svenpetersen1965/C64-Diagnostic-Rev.-586220-Harness/Diag586220_Harness/C128_Keyboard_PCB/Rev. 1/Text/145_cover_sheet.docx

Project Documentation

C128 Diagnostic – Keyboard PCB

Project number: 145

Revision: 1

Date: 15.05.2020
