svenpetersen1965/C64-Diagnostic-Rev.-586220-Harness/Diag586220_Harness/Diag586220_Keyboard_ext/Rev. 0/Texts/Diag586220_Keyb_Ext_ModD.docx

Diagnostic 586220 Harness - Keyboard Dongle Extended Rev. 0

Module Description

# Introduction

The extended Keyboard Dongle is meant to be an extension to existing Diagnostic Harnesses. It prevents the false OK when testing the control ports, while the keyboard PCB is inserted. This is accomplished by analog switches for the feedbacks, that are in common with the joystick signals on the control ports.

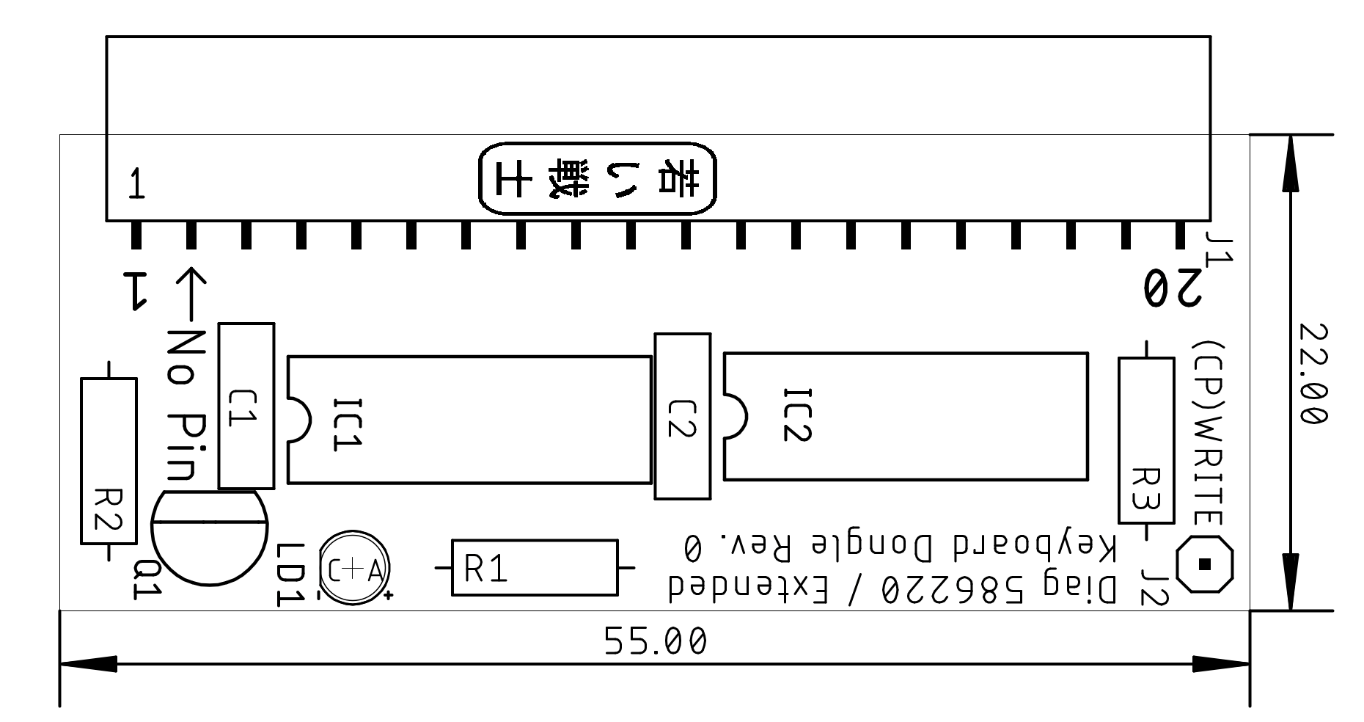
[picture p32: figure]

Figure 1: Dimensions of the PCB

The extended Keyboard Dongle for Diagnostic 586220 provides the required feedback connections for testing the C64’s CIA U1, which the keyboard is connected to. An LED serves as an alternative power and operation indicator. It is normally on and switches off while testing the Control Ports.

The Restore key is connected to a dedicated line and is not tested.

What does Extended Keyboard PCB do better than the normal keyboard PCB?

As long as the old keyboard dongle is connected to the keyboard header, the feedbacks bridge the analog switches for testing the control ports. These analog switches are found on the User Port PCB. They are inside the two 4066 ICs there.

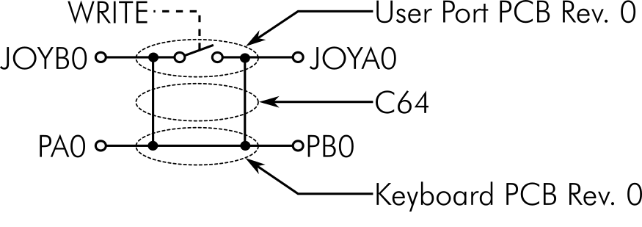
[picture p33: figure]

Figure 2: Test situation with the original diagnostic harness

For properly testing the control ports, the keyboard dongle has to be removed. This way, the test actually requires two passes. Otherwise, the control ports are tested improperly. A broken trace to the control port or a defective port connector would not be detected.

The extended Keyboard Dongle provides switched feedbacks for the signals, that are shared with the joysticks.

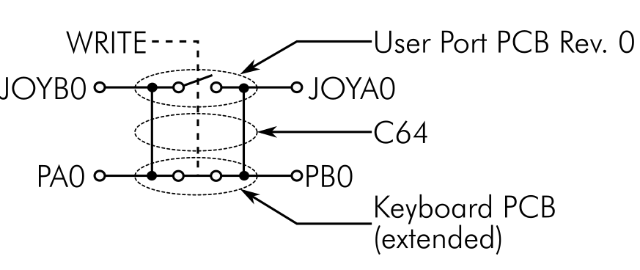
[picture p34: figure]

Figure 3: Test situation with the extended Keyboard Dongle

These are PB0«PA0, PB1«PA1, PB2«PA2, PB3«PA3 and PB4«PA4. The switches are opened by a (cassette port) WRITE signal going high, which also closes the connection on the user port dongle at the same time. The reason is, that

This WRITE signal is generated via a voltage divider on the user Port Dongle, which is also fed back to the Cassette Port Dongle. It can be found on Pin 5 of the cassette edge connector (on every kind of test harness). An existing harness can be easily modified by soldering a 40cm Dupont cable to the indicated Pin (refer to Figure 4), which is then connected to J2 (one pin) of the extended Keyboard Dongle.

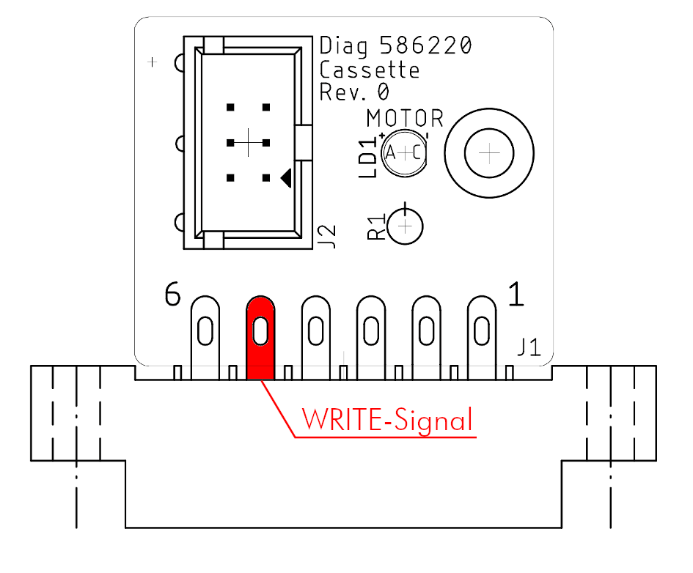
[picture p35: figure]

Figure 4: Locating the Write signal

In case this cable is not connected, the extended Keyboard Dongle works like a normal keyboard dongle. The analog switches are closed in this case. The open state of the switches is indicated by the LED, which is off while testing the control ports (this needs to be observed).

The extended Keyboard Dongle works with all versions of the standard Diagnostic 586220 software. A modification of the software is not required.

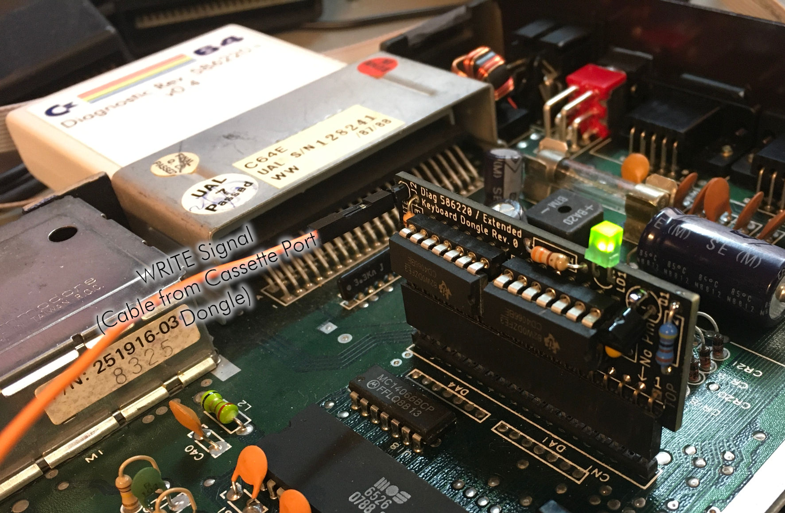
[picture p36: figure]

Figure 5: The Extended Keyboard Dongle on an ASSY 250469

# Connections

J1: 20p receptacle (pitch 2.54mm)

Pin | Signal | | Signal | Pin
5 | PB3 | « | PA3 | 17
6 | PB6 | « | PA6 | 14
7 | PB5 | « | PA5 | 15
8 | PB4 | « | PA4 | 16
9 | PB7 | « | PA7 | 20
10 | PB2 | « | PA2 | 18
11 | PB1 | « | PA1 | 19
12 | PB0 | « | PA0 | 13

J2: Single pin (DuPont). Input for the WRITE signal from the Cassette Port (Dongle).

Diag586220_Keyb_Ext_ModD.docx 10.03.2020 20:10 Drafted by Sven Petersen Page 2 of 2 Doc.-No.: 143-6-01-00

Diag586220_Keyb_Ext_ModD.docx 10.03.2020 20:10 Drafted by Sven Petersen Page 1 of 1 Doc.-No.: 143-6-01-00
