svenpetersen1965/C64-Diagnostic-Rev.-586220-Harness/Diag586220_Harness/Diag586220_Keyboard_ext/Rev. 0/Texts/143_cover_sheet.docx

Project Documentation

Diagnostic Rev. 586220 – Extended Keyboard Dongle

Project number: 143

Revision: 0

Date: 16.02.2020
