svenpetersen1965/C64-Diagnostic-Rev.-586220-Harness/Diag586220_Harness/C128_Keyboard_PCB/SMD_Rev. 1/Pictures/dimensions.png

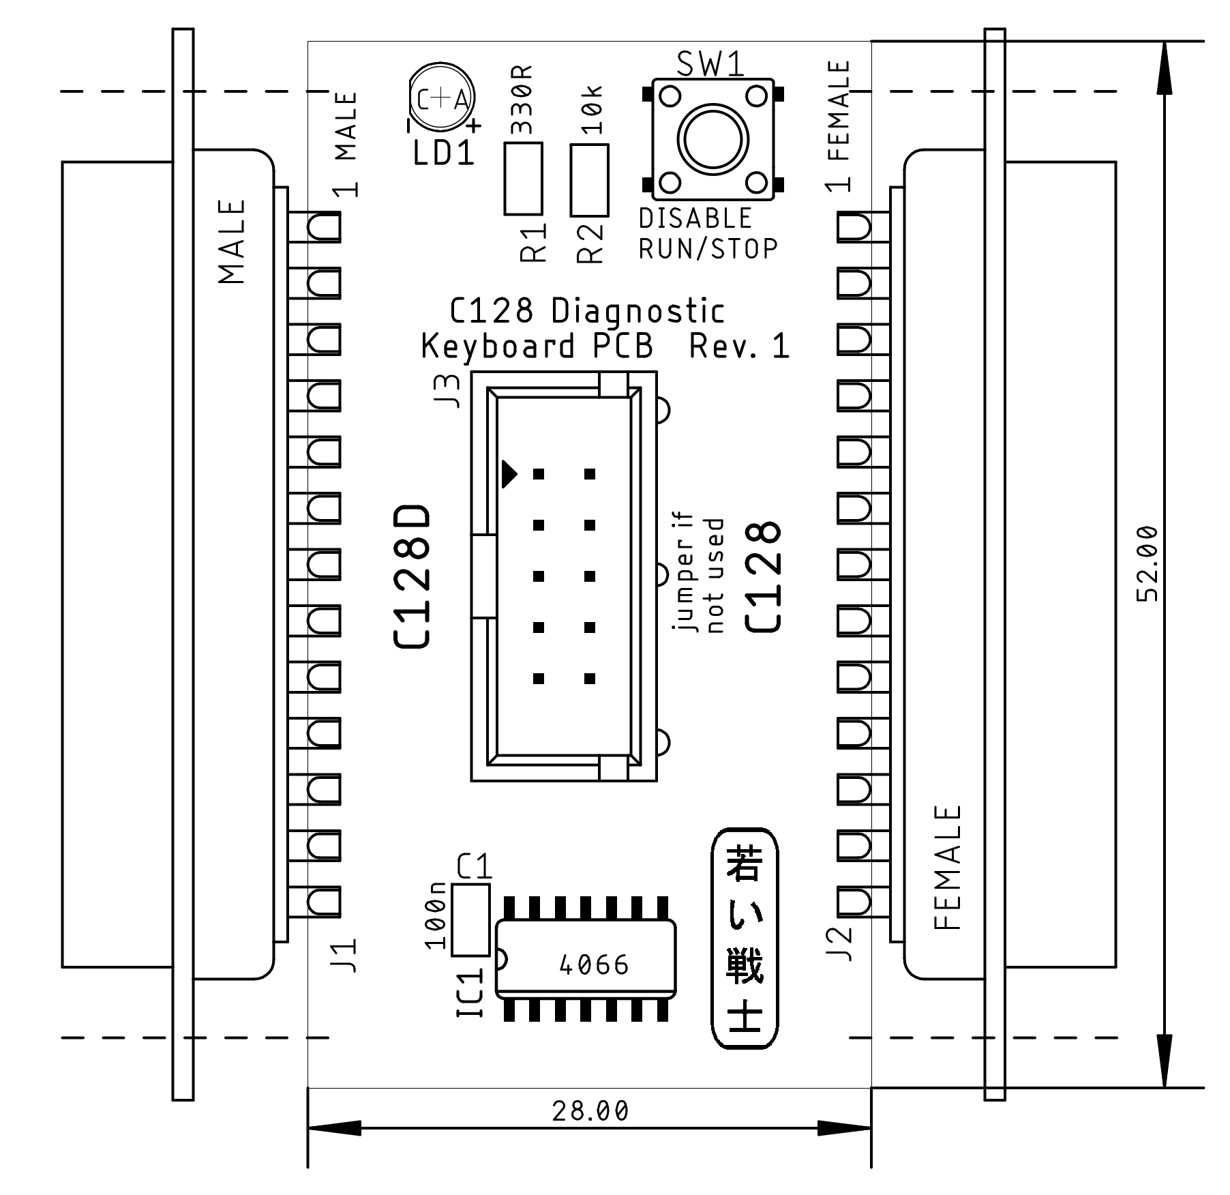
Diag586220_Harness/C128_Keyboard_PCB/SMD_Rev. 1/Pictures/dimensions.png
