svenpetersen1965/C64-Diagnostic-Rev.-586220-Harness/Diag586220_Harness/Case_3D_Data/Cassette Port/Rev. 0/picture/Diag_CP v5.png

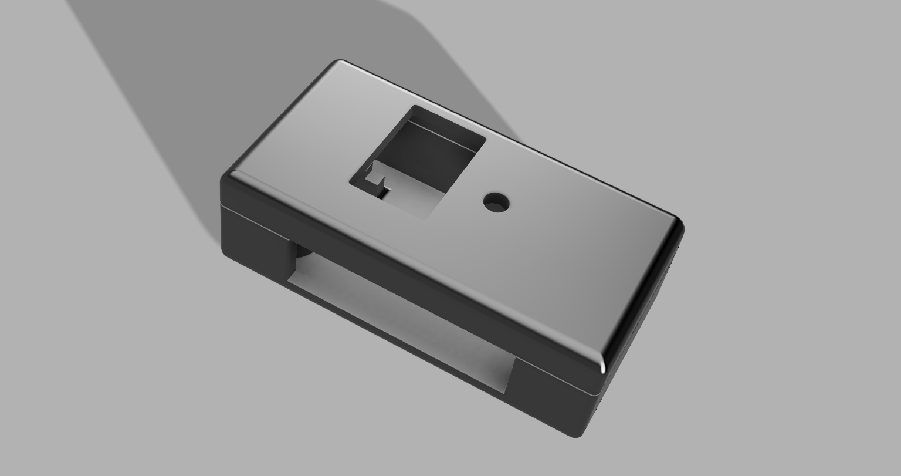
Diag586220_Harness/Case_3D_Data/Cassette Port/Rev. 0/picture/Diag_CP v5.png
