svenpetersen1965/C64-Diagnostic-Rev.-586220-Harness/Diag586220_Harness/Case_3D_Data/Label/Rev. 0/Inkscape/Case_Labels.png

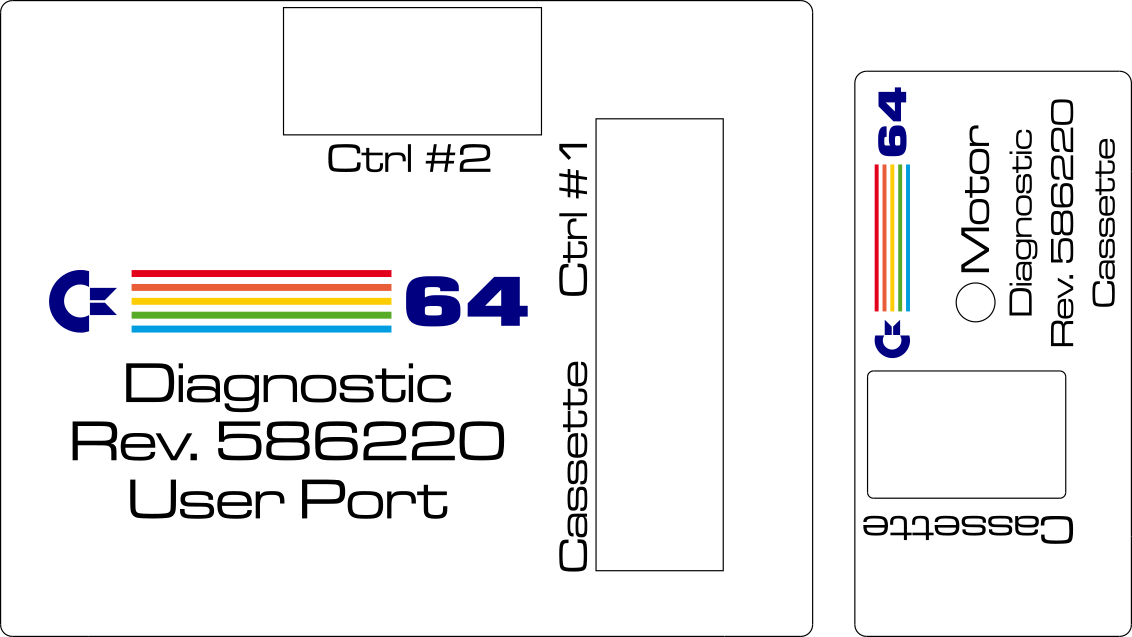
Diag586220_Harness/Case_3D_Data/Label/Rev. 0/Inkscape/Case_Labels.png
