svenpetersen1965/C64-Diagnostic-Rev.-586220-Harness/Diag586220_Harness/Case_3D_Data/Label/Rev. 1/Rev. 1.0/picture/user_port_label.png

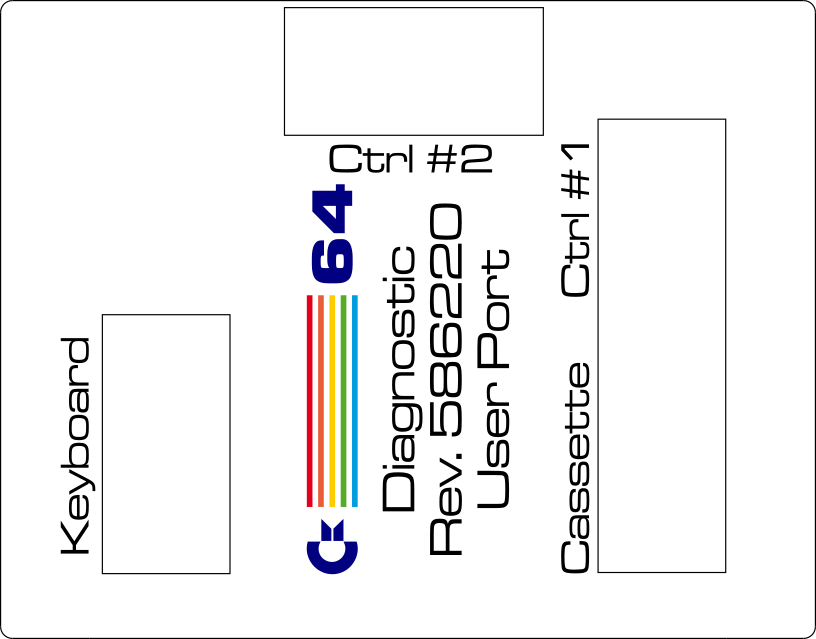
Diag586220_Harness/Case_3D_Data/Label/Rev. 1/Rev. 1.0/picture/user_port_label.png
