svenpetersen1965/C64-Diagnostic-Rev.-586220-Harness/Diag586220_Harness/Case_3D_Data/Label/Rev. 1/Rev. 1.1/picture/case labels.png

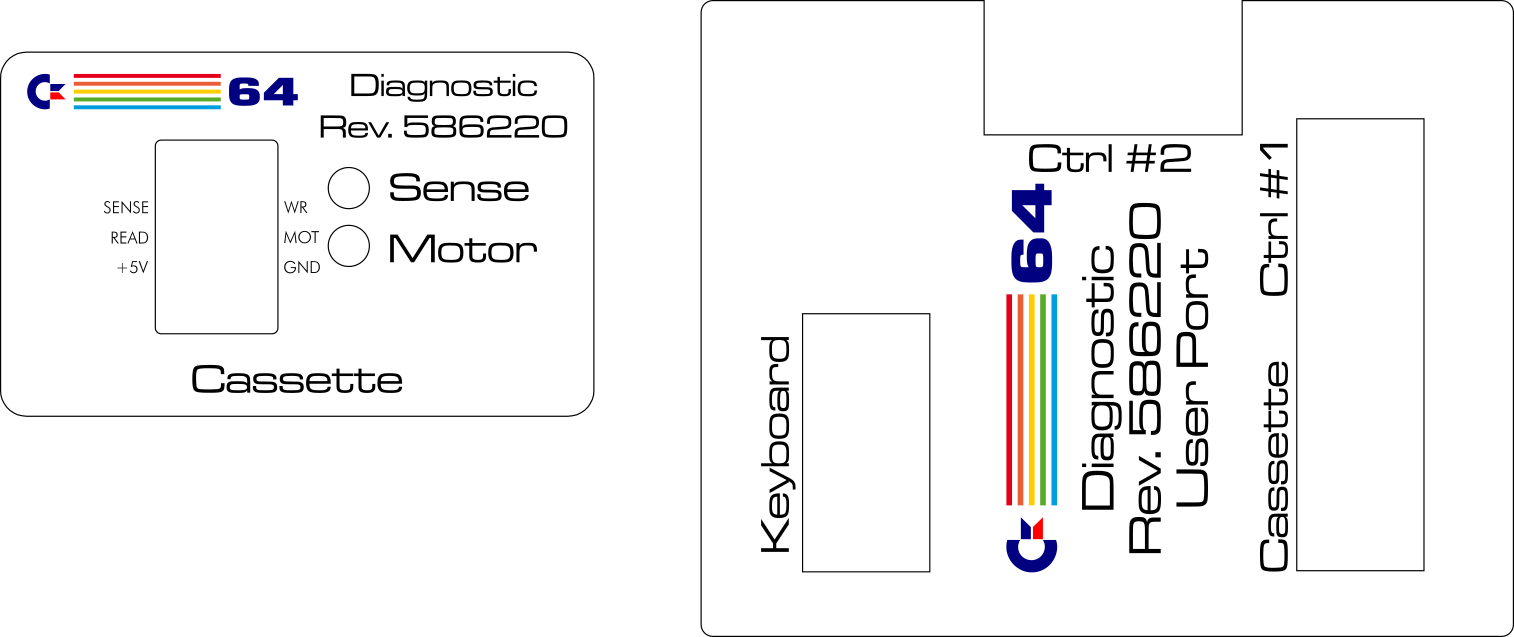
Diag586220_Harness/Case_3D_Data/Label/Rev. 1/Rev. 1.1/picture/case labels.png
