svenpetersen1965/C64-Diagnostic-Rev.-586220-Harness/Diag586220_Harness/Case_3D_Data/Label/Rev. 3/Pictures/label_VM.png

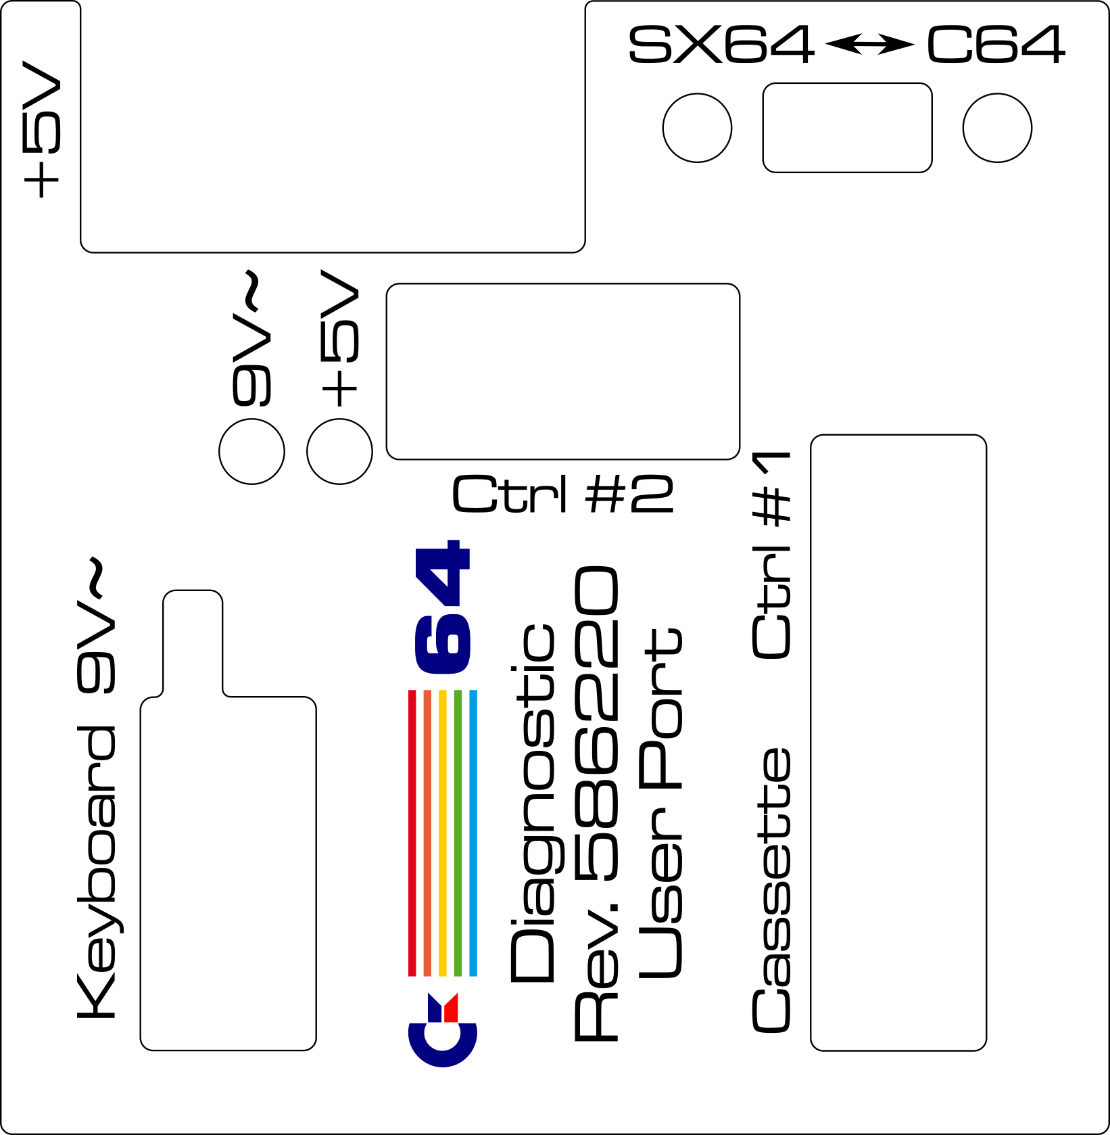
Diag586220_Harness/Case_3D_Data/Label/Rev. 3/Pictures/label_VM.png
