svenpetersen1965/C64-Diagnostic-Rev.-586220-Harness/Diag586220_Harness/Case_3D_Data/User Port/Rev. 0/Picture/Diag_UP v8.png

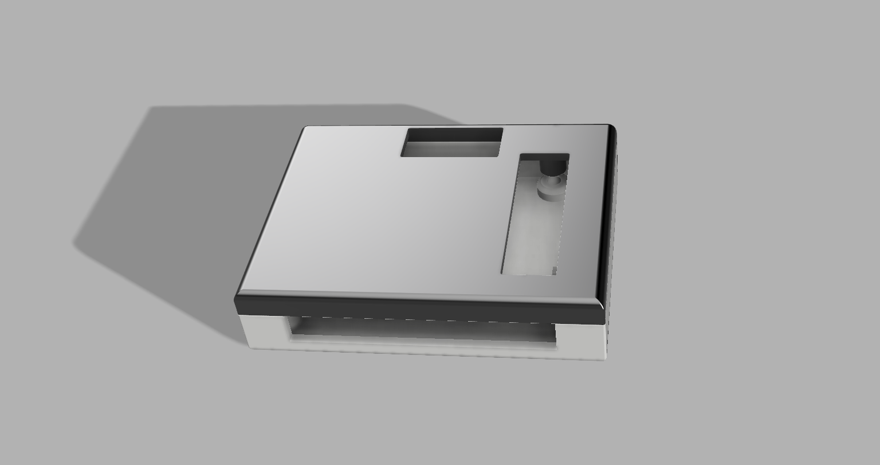
Diag586220_Harness/Case_3D_Data/User Port/Rev. 0/Picture/Diag_UP v8.png
