svenpetersen1965/C64-Diagnostic-Rev.-586220-Harness/Diag586220_Harness/Case_3D_Data/User Port/Rev. 3/Inkscape/7segVM.png

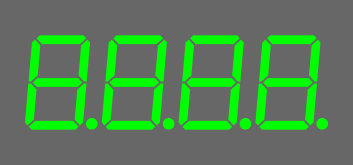
Diag586220_Harness/Case_3D_Data/User Port/Rev. 3/Inkscape/7segVM.png
