svenpetersen1965/C64-Diagnostic-Rev.-586220-Harness/Diag586220_Harness/Case_3D_Data/User Port/Rev. 3/pictures/Diag_UP_PCB_v3 v24.png

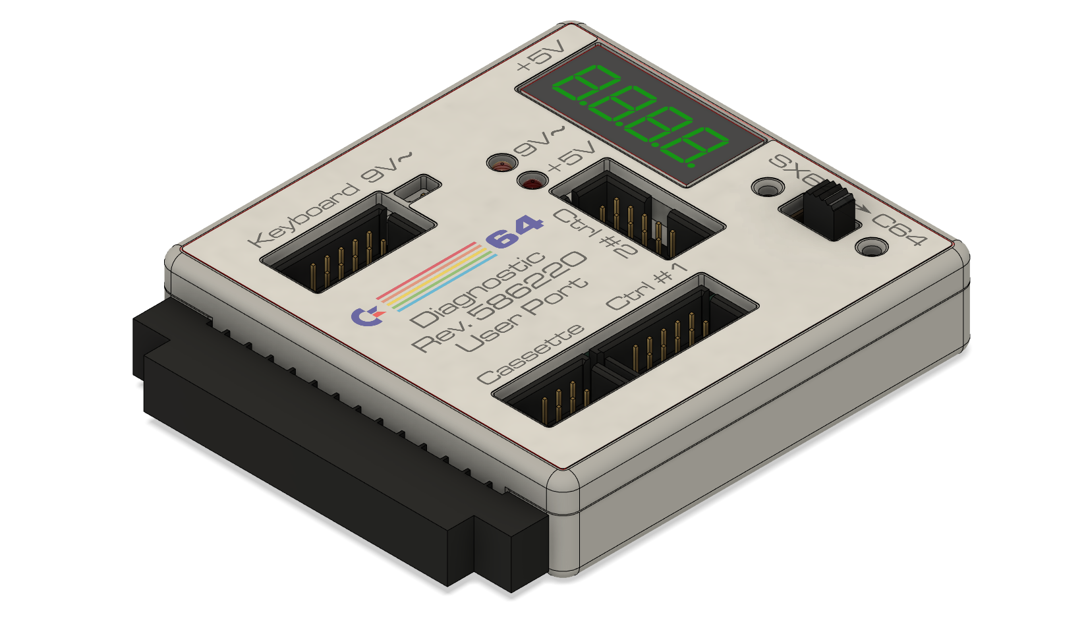
Diag586220_Harness/Case_3D_Data/User Port/Rev. 3/pictures/Diag_UP_PCB_v3 v24.png
