svenpetersen1965/C64-Diagnostic-Rev.-586220-Harness/Diag586220_Harness/Diag586220_Cassette_Port/SMD_Rev.1/pictures/cassette_pcb.png

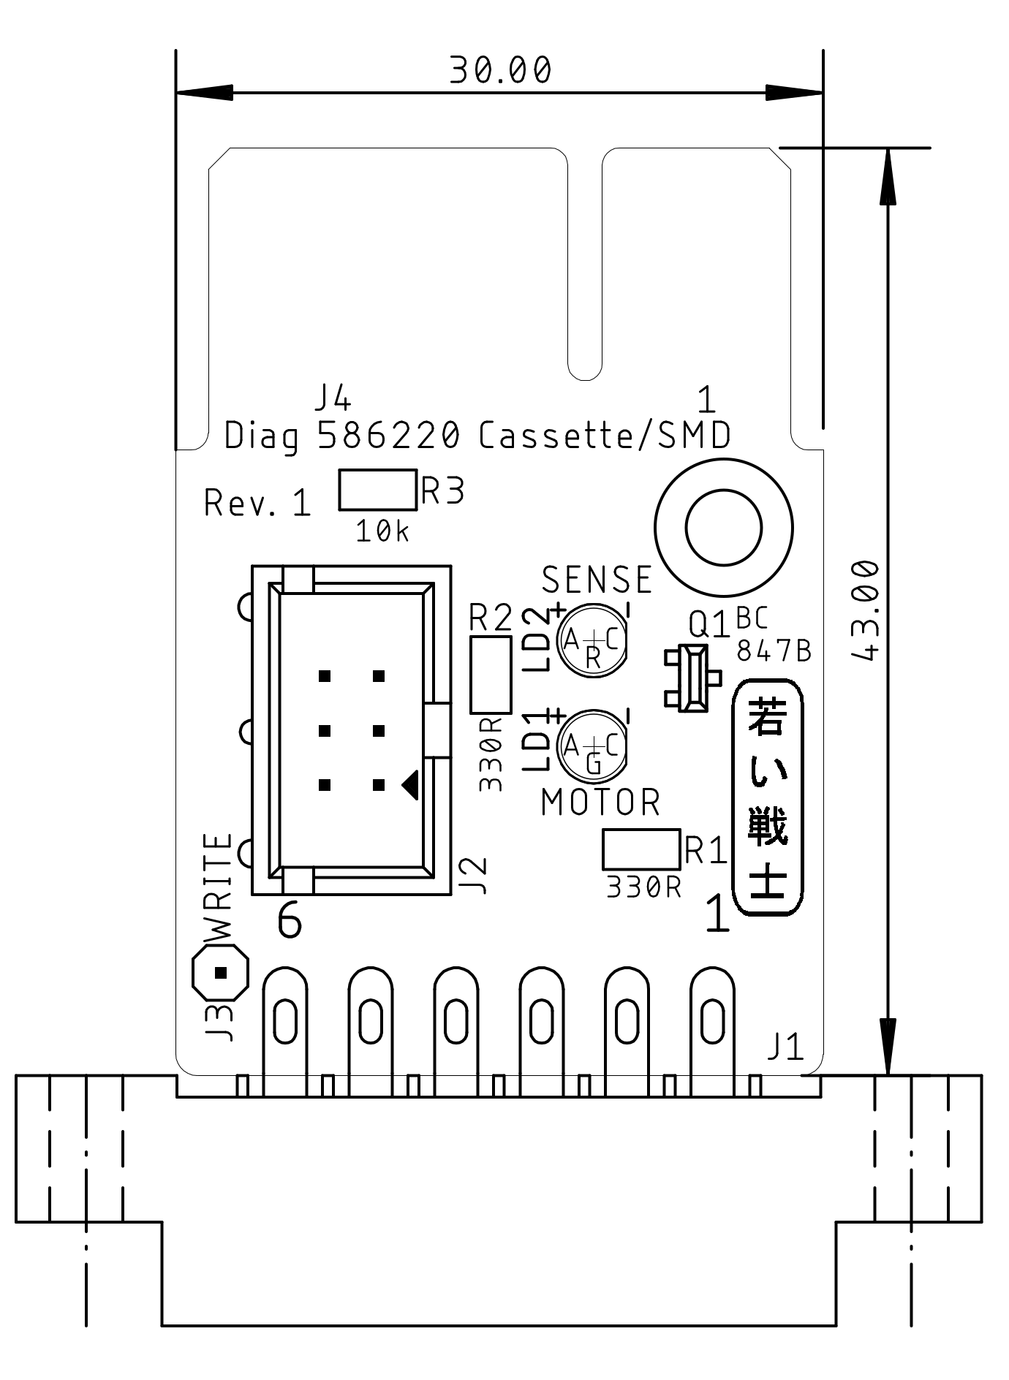
Diag586220_Harness/Diag586220_Cassette_Port/SMD_Rev.1/pictures/cassette_pcb.png
