svenpetersen1965/C64-Diagnostic-Rev.-586220-Harness/Diag586220_Harness/Diag586220_Keyboard_ext/Rev. 0/pictures/4032_-_Modification_Rev_0.JPG

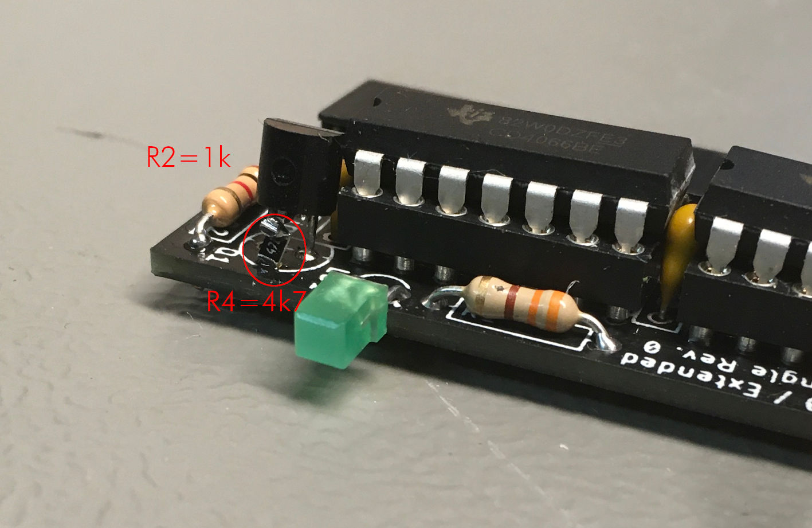
Diag586220_Harness/Diag586220_Keyboard_ext/Rev. 0/pictures/4032_-_Modification_Rev_0.JPG
