svenpetersen1965/C64-Diagnostic-Rev.-586220-Harness/Diag586220_Harness/Diag586220_Keyboard_ext/Rev. 1/Texts/4199_-_Ext_KB_Dongle_Rev1.JPG

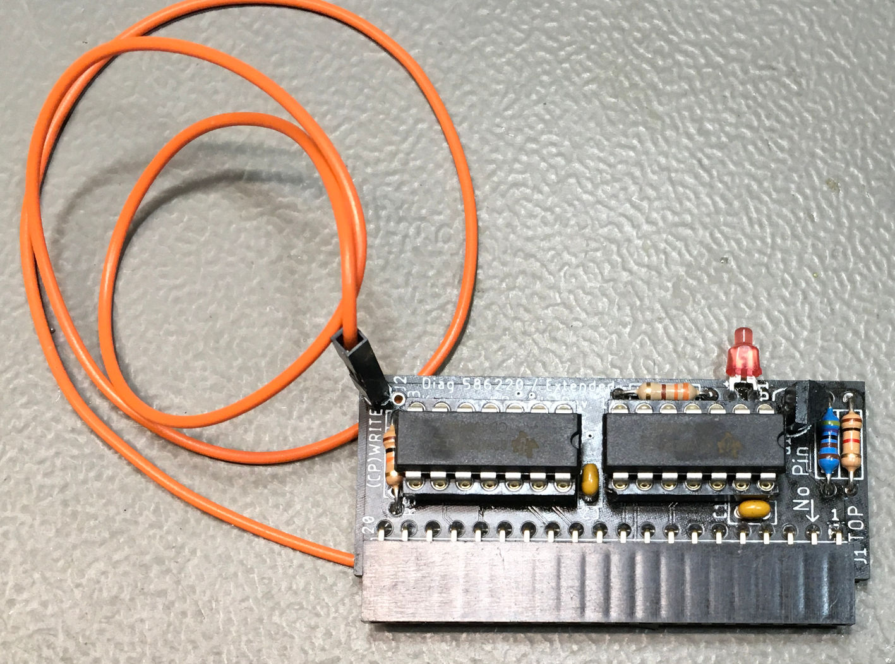
Diag586220_Harness/Diag586220_Keyboard_ext/Rev. 1/Texts/4199_-_Ext_KB_Dongle_Rev1.JPG
