svenpetersen1965/C64-Diagnostic-Rev.-586220-Harness/Diag586220_Harness/Diag586220_User_Port/Rev.3/AutoSketch/IEC-Dongle.gif

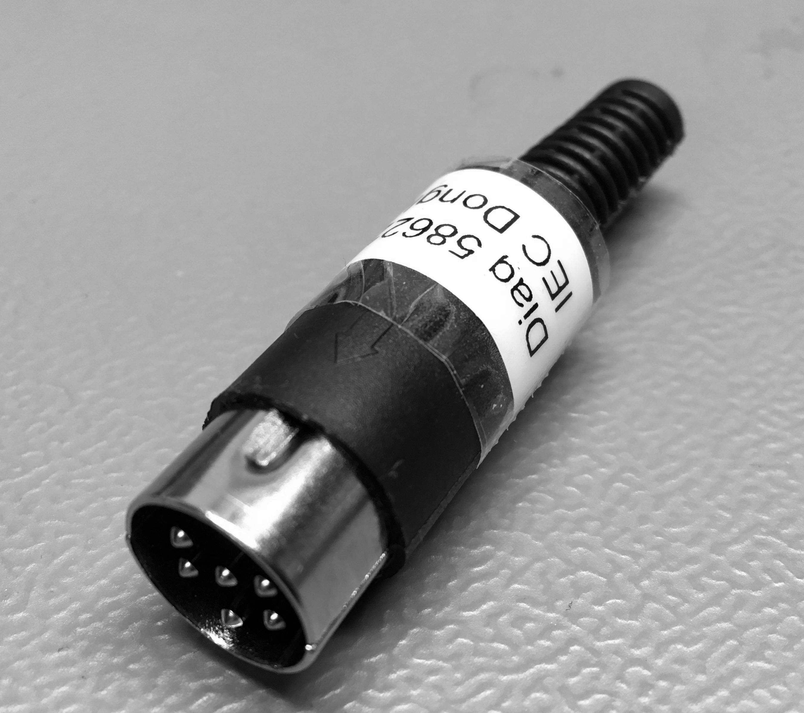
Diag586220_Harness/Diag586220_User_Port/Rev.3/AutoSketch/IEC-Dongle.gif
