svenpetersen1965/C64-Diagnostic-Rev.-586220-Harness/Diag586220_Harness/Diag586220_User_Port/Rev.3/pictures/1520_-_4digit_VM_in_situ.JPG

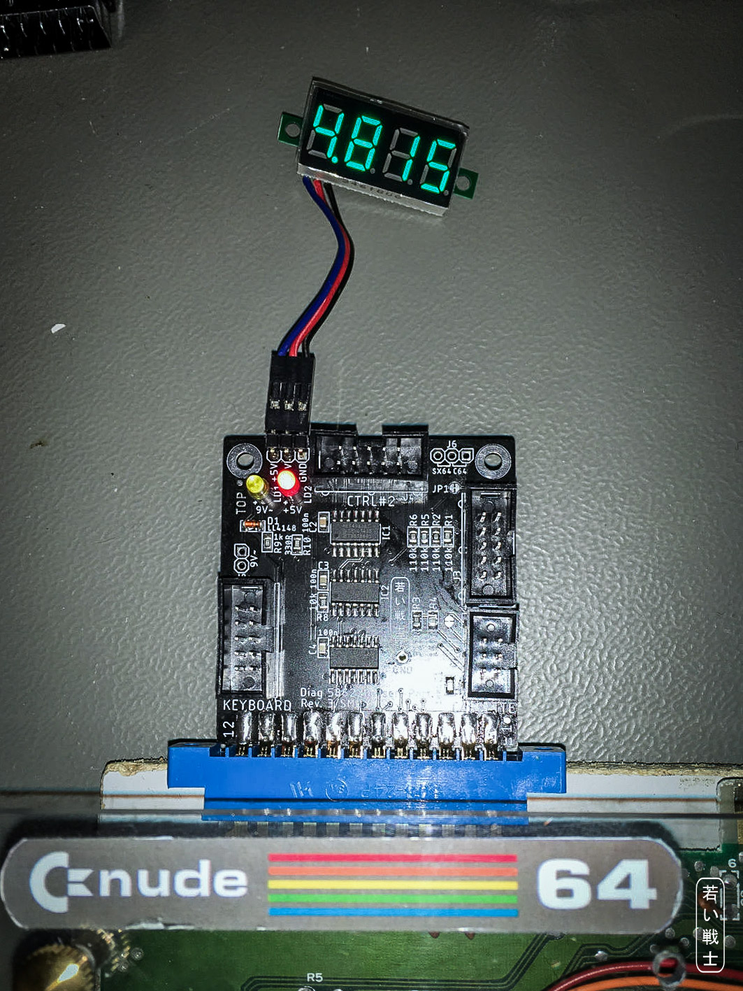
Diag586220_Harness/Diag586220_User_Port/Rev.3/pictures/1520_-_4digit_VM_in_situ.JPG
