svenpetersen1965/C64-Diagnostic-Rev.-586220-Harness/Diag586220_Harness/Diag586220_User_Port/Rev.3/pictures/4961_-_C64_Diagnostic_Harvness_VM.JPG

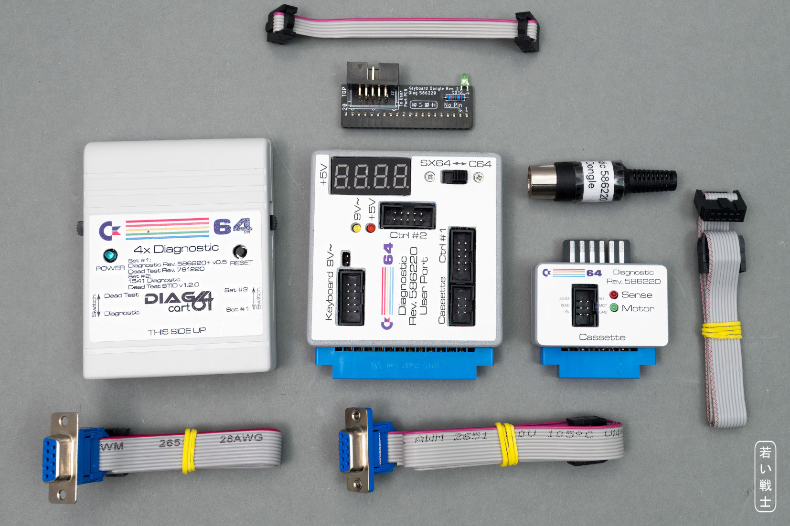
Diag586220_Harness/Diag586220_User_Port/Rev.3/pictures/4961_-_C64_Diagnostic_Harvness_VM.JPG
