svenpetersen1965/C64-Diagnostic-Rev.-586220-Harness/Diag586220_Harness/Diag586220_User_Port/Rev.3/pictures/9290_-_case_with_SX64C64_Jumper_configuration.JPG

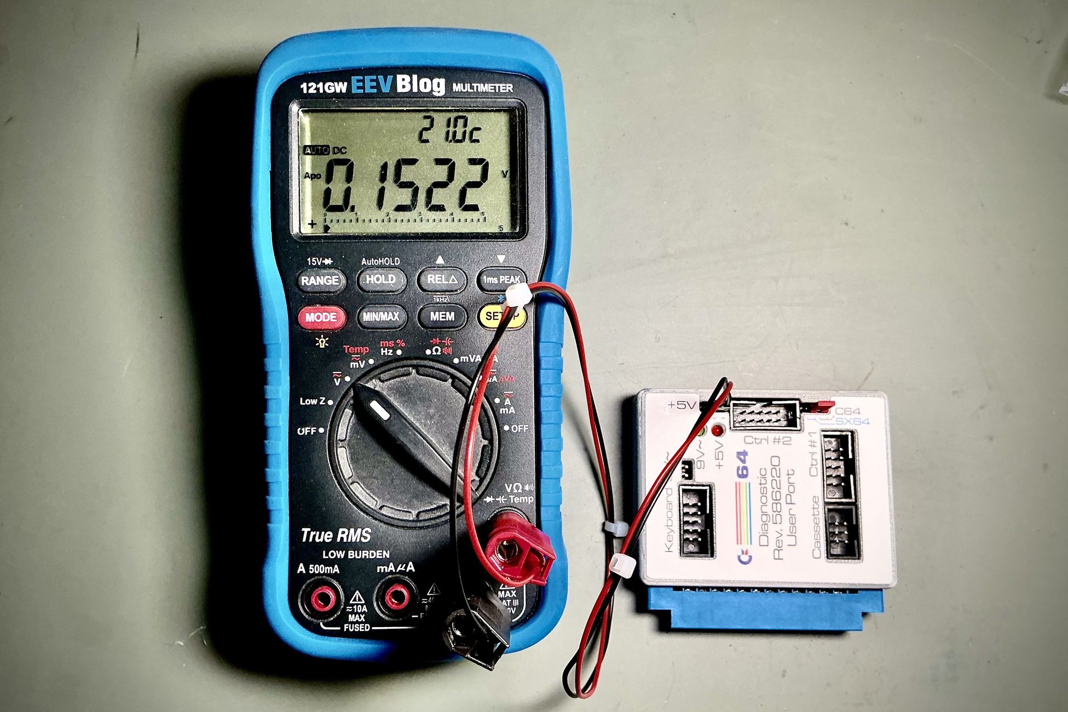
Diag586220_Harness/Diag586220_User_Port/Rev.3/pictures/9290_-_case_with_SX64C64_Jumper_configuration.JPG
