svenpetersen1965/C64-Diagnostic-Rev.-586220-Harness/Diag586220_Harness/Diag586220_User_Port/SMD_Rev.3/pictures/IMG_2500_1.JPG

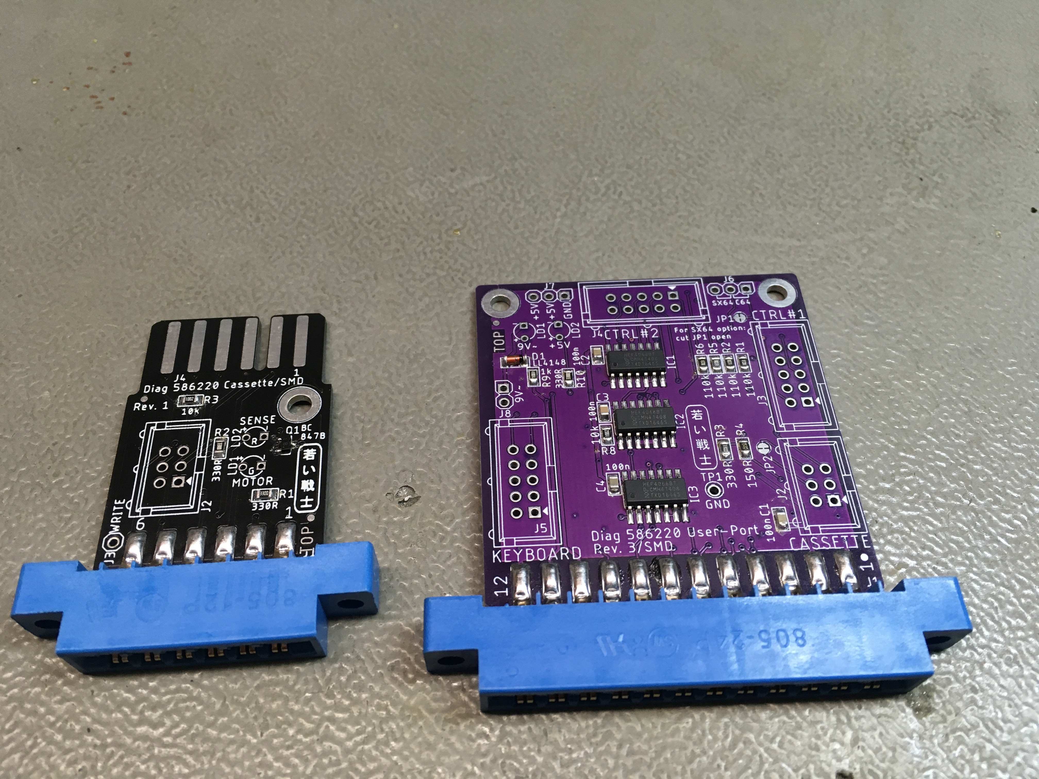
Diag586220_Harness/Diag586220_User_Port/SMD_Rev.3/pictures/IMG_2500_1.JPG
