svenpetersen1965/C64-Diagnostic-Rev.-586220-Harness/Diag586220_Harness/calculation/Diag_Harness_Rev1_complete_calc.xlsx

Calculation Diagnostic Harness Rev. 1
Pos. | Qty | Value | €/ea | € | Comment
1 | 1 | Cassette Port Dongle | 1.00 € | 1.00 € | 2 layer, Cu 35µ, HASL, 30.0mm x 25.0mm, 1.6mm FR4
2 | 1 | 2x6, 3.96mm pitch | 3.00 € | 3.00 € | edge connector, C64 cassette port
3 | 1 | 2x3 box connector | 0.19 € | 0.19 € | e.g. Reichelt WSL 6G
4 | 1 | 3mm/green | 0.20 € | 0.20 € | LED, 3mm, green
5 | 1 | 3mm/red | 0.20 € | 0.20 € | LED, 3mm, red
6 | 1 | BC546B | 0.10 € | 0.10 € | Transistor
7 | 2 | 10k | 0.10 € | 0.20 € | 1/4 Watt, 5%
8 | 1 | 330R | 0.10 € | 0.10 € | 1/4 Watt, 5%
 |  |  |  | 4.99 €
Pos. | Qty | Value | €/ea | € | Comment
1 | 1 | User Port Dongle | 1.00 € | 1.00 € | 2 layer, Cu 35µ, HASL, LLL x BBB, 1.6mm FR4
2 | 1 | 2x3 box connector | 0.19 € | 0.19 € | e.g. Reichelt WSL 6G
3 | 3 | 2x5 box connector | 0.10 € | 0.30 € | e.g. Reichelt WSL 10G
4 | 1 | 0R | 0.10 € | 0.10 € | 0 Ohm bridge
5 | 4 | 100n/50V | 0.20 € | 0.80 € | cer. cap, 2.5mm pitch
6 | 4 | 110k | 0.10 € | 0.40 € | 1/4W, 1%
7 | 1 | 150R | 0.10 € | 0.10 € | 1/4W, 5%
8 | 1 | 320R | 0.10 € | 0.10 € | 1/4W, 5% (316W works, 330W should work as well)
9 | 3 | HCF4066B | 0.67 € | 2.01 € | ST Micro or equivalent
10 | 3 | DIL 14 | 0.23 € | 0.69 € | DIL IC sockets
11 | 1 | 2x12, 3.96mm pitch | 3.00 € | 3.00 € | edge connector, C64 user port
12 | 3 | TP 1pin | 0.00 € | 0.00 € | Pin Header, e.g. Reichelt RND 205-00622
13 | 170 | 10p/AWG28/1,27mm | 0.01 € | 0.85 € | Ribbon Cable
14 | 2 | 6p IDC receptable, 2,54mm | 0.63 € | 1.26 € | e.g. Reichelt RND 205-00680
15 | 4 | 10p IDC receptable, 2,54mm | 0.25 € | 1.00 € | e.g. Reichelt RND 205-00682
16 | 2 | 9p D-SUB (female), IDC | 0.66 € | 1.32 € | e.g. Reichelt D-SUB BU 09FB
17 | 1 | DIN-plug 6p | 0.26 € | 0.26 € | e.g. Reichelt MAS 60
18 | 4 | Wire 0,25mm², red | 0.00 € | 0.00 € | wire, color what ever
 |  |  |  | 13.38 €
Pos. | Qty | Value | €/ea | € | Comment
1 | 1 | Keyboard Dongle | 1.00 € | 1.00 € | 2 layer, Cu 35µ, HASL, 53.0mm x 14.0mm, 1.6mm FR4
2 | 1 | BL1-85AXX-20U | 0.45 € | 0.45 € | e.g. MPE Garry, Reichelt BL 1x20W8 2,54
3 | 1 | 3mm/green | 0.20 € | 0.20 € | LED
4 | 1 | 2x5 box connector | 0.10 € | 0.10 € | e.g. Reichelt WSL 10G
5 | 1 | 330R | 0.10 € | 0.10 € | 1/4 Watt, 5%
 |  |  |  | 1.85 €
Pos. | Qty | Value | €/ea | € | Comment
1 | 1 | C128 Keyboard Dongle | 1.00 € | 1.00 € | 2 layer, Cu 35µ, HASL, 28.0 x 48.0mm, 1.6mm FR4
2 | 1 | 2x5pin box header, 2.54mm pitch | 0.10 € | 0.10 € | e.g. Reichelt.de: WSL 10G.
3 | 1 | LED 3mm, green | 0.20 € | 0.20 € | LED, standard
4 | 1 | 330R | 0.10 € | 0.10 € | Resistor, 0.25W, 5% or better
5 | 1 | DB25F/EDGE | 0.22 € | 0.22 € | DSub 25, female, solder cups, e.g. Reichelt.de: D-SUB BU 25
6 | 1 | DB25M/EDGE | 0.26 € | 0.26 € | DSub 25, male, solder cups, e.g. Reichelt.de: D-SUB ST 25
7 | 1 | 10k | 0.10 € | 0.10 € | Resistor, 0.25W, 5% or better
8 | 1 | JTP-1130 | 0.15 € | 0.15 € | Standard 6x6mm tact switch, e.g. Namae JTP-1130 or any other
9 | 1 | HCF4066B | 0.67 € | 0.67 € | ST Micro or equivalent (4066)
10 | 1 | DIL 14 | 0.23 € | 0.23 € | DIL IC sockets
11 | 1 | 100n/50V | 0.20 € | 0.20 € | cer. cap, 2.5mm pitch
 |  |  |  | 3.23 €
