svenpetersen1965/C64-Diagnostic-Rev.-586220-Harness/Diag586220_Harness/Diag586220_User_Port/Rev.3/excel/Diag586220_UserPort_calc_v3_0.xlsx

Diagnostic Rev. 586220 Harness - User Port Rev. 3
Bill of Material Rev. 3.0
Pos. | Qty | Value | €/ea | € | Comment
1 | 1 | 113-2-01-03 | 1.00 € | 1.00 € | 2 layer, Cu 35µ, HASL, LLL x BBB, 1.6mm FR4
2 | 1 | 2x3 box connector | 0.29 € | 0.29 € | e.g. Reichelt WSL 6G
3 | 3 | 2x5 box connector | 0.11 € | 0.33 € | e.g. Reichelt WSL 10G
4 | 0 | ~~0R~~ | 0.10 € | ~~0.00 €~~ | removed in Rev. 3
5 | 4 | 100n/50V | 0.20 € | 0.80 € | cer. cap, 2.5mm pitch
6 | 4 | 110k | 0.10 € | 0.40 € | 1/4W, 1%
7 | 1 | 150R | 0.10 € | 0.10 € | 1/4W, 5%
8 | 1 | 316R | 0.10 € | 0.10 € | 1/4W, 5% (316W works, 330W should work as well)
9 | 3 | HCF4066B | 0.67 € | 2.01 € | ST Micro or equivalent
10 | 3 | DIL 14 | 0.44 € | 1.32 € | DIL IC sockets
11 | 1 | 2x12, 3.96mm pitch | 3.00 € | 3.00 € | edge connector, C64 user port
12 | 0 | TP 1pin | 0.00 € | 0.00 € | optional, Pin Header, e.g. Reichelt RND 205-00622
13 | 1 | 1.82m10p/AWG28/1,27mm | 2.15 € | 2.15 € | Ribbon Cable
14 | 2 | 6p IDC receptable, 2,54mm | 0.26 € | 0.52 € | e.g. Reichelt RND 205-00680
15 | 4 | 10p IDC receptable, 2,54mm | 0.11 € | 0.44 € | e.g. Reichelt RND 205-00682
16 | 2 | 9p D-SUB (female), IDC | 0.63 € | 1.26 € | e.g. Reichelt D-SUB BU 09FB
17 | 1 | DIN-plug 6p | 0.47 € | 0.47 € | e.g. Reichelt MAS 60
18 | 1 | 4cm Wire 0,25mm², red | 0.10 € | 0.10 € | wire, color what ever
19 | 1 | 10k | 0.10 € | 0.10 € | 1/4W, 5%
20 | 1 | 3x1pin, 2.54mm | 0.08 € | 0.08 € | optional pin header, 2.54mm pitch
21 | 1 | T217 | 0.45 € | 0.45 € | option. Toggle Switch can be connected alternatively
22 | 1 | cut pad | 0.00 € | 0.00 € | not part, it is on the PCB. Closed by default for C64. For switching, cut open
23 | 1 | 1x3p., 2.54mm | 0.00 € | 0.00 € | solderpads for voltmeter (see discription)
24 | 1 | 1x2p., 2.54mm | 0.08 € | 0.08 € | do not place (see discription)
25 | 2 | 3mm, green | 0.14 € | 0.28 € | standard LED
26 | 1 | 1N4148 | 0.03 € | 0.03 € | diode
27 | 1 | 1k | 0.10 € | 0.10 € | 1/4W, 5%
28 | 1 | 330R | 0.10 € | 0.10 € | 1/4W, 5%
 |  | Total |  | 15.51 €
 |  | Voltmeter 4 digit, prec. | 1,80 | 1.80 €
 |  |  |  | 17.31 €
