svenpetersen1965/C64-Diagnostic-Rev.-586220-Harness/Diag586220_Harness/Diag586220_Keyboard_ext/Rev. 0/dxf/C64_Keyb-Test-ext.dxf

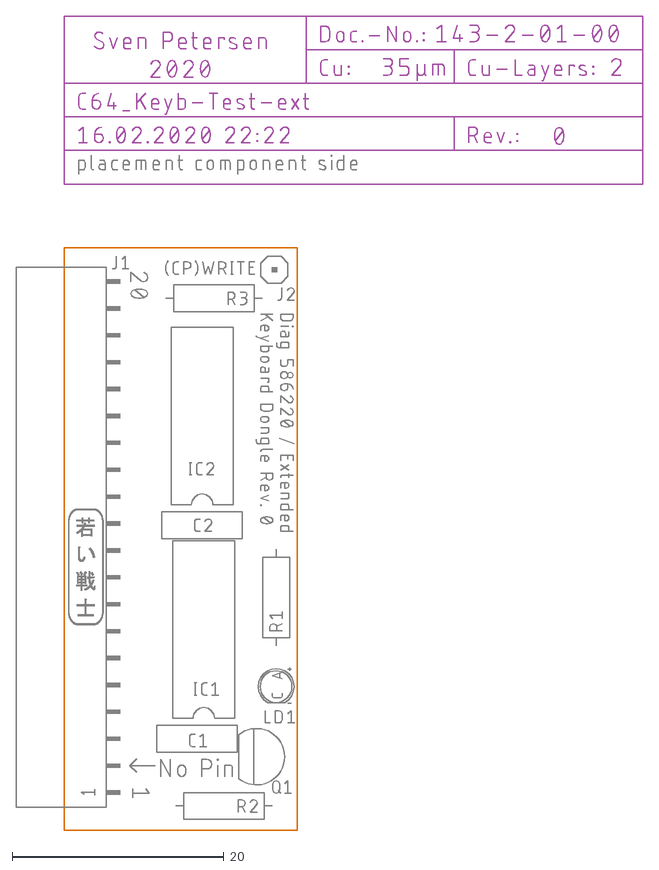
[picture p125: CAD file, 2020-03-11]
Diag586220_Harness/Diag586220_Keyboard_ext/Rev. 0/dxf/C64_Keyb-Test-ext.dxf
59.1 x 76.9
