svenpetersen1965/C64-Diagnostic-Rev.-586220-Harness/Diag586220_Harness/Diag586220_User_Port/Rev.3/dxf/C64_Userport_Test.dxf

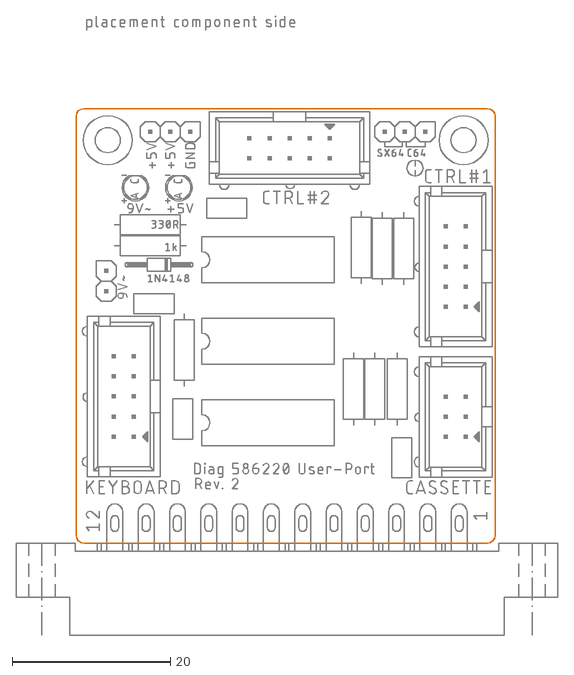
[picture p127: CAD file, 2024-05-25]
Diag586220_Harness/Diag586220_User_Port/Rev.3/dxf/C64_Userport_Test.dxf
68.5 x 78.3
