svenpetersen1965/C64-Diagnostic-Rev.-586220-Harness/Diag586220_Harness/Diag586220_User_Port/SMD_Rev.3/dxf/C64_Userport_Test_SMD.dxf

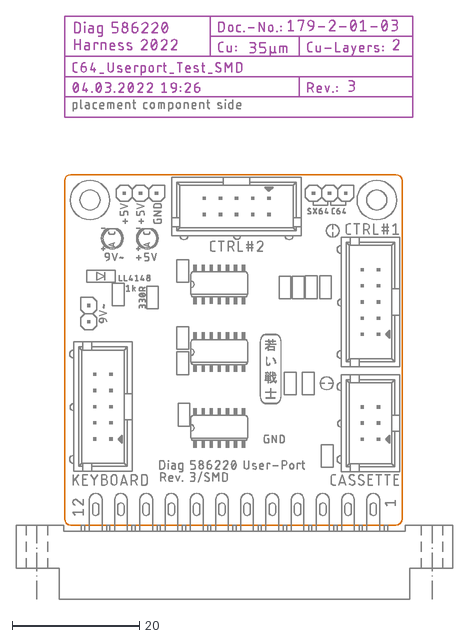
[picture p128: CAD file, 2024-05-25]
Diag586220_Harness/Diag586220_User_Port/SMD_Rev.3/dxf/C64_Userport_Test_SMD.dxf
68.5 x 91.5
