svenpetersen1965/C64-Diagnostic-Rev.-586220-Harness/Diag586220_Harness/Case_3D_Data/Cassette Port/Rev. 0/STL/bottom shell CP.stl

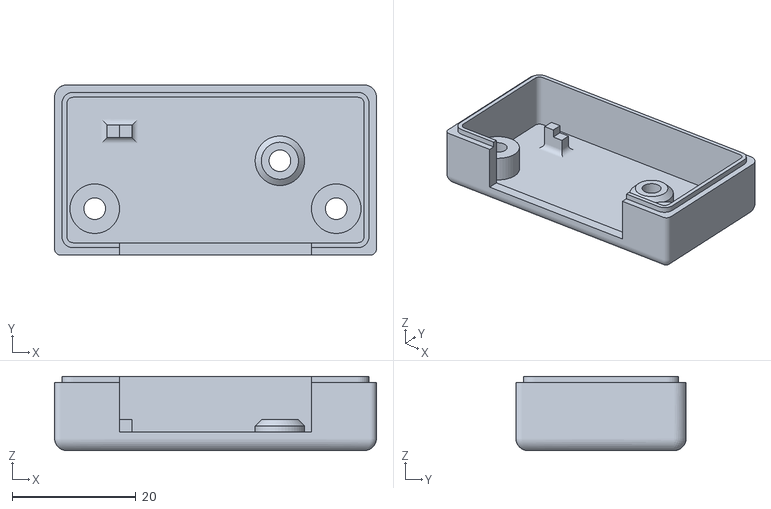
[picture p129: CAD file, 2019-09-12]
Diag586220_Harness/Case_3D_Data/Cassette Port/Rev. 0/STL/bottom shell CP.stl
52.0 x 27.5 x 12.0
