svenpetersen1965/C64-Diagnostic-Rev.-586220-Harness/Diag586220_Harness/Case_3D_Data/User Port/Rev. 0/stl/spacer (1.9mm).stl

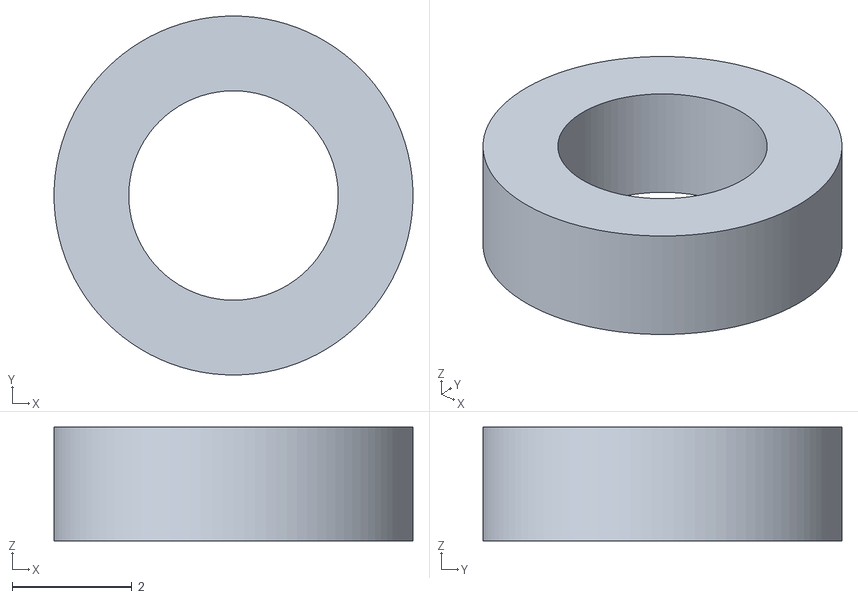
[picture p130: CAD file, 2020-03-15]
Diag586220_Harness/Case_3D_Data/User Port/Rev. 0/stl/spacer (1.9mm).stl
6.00 x 6.00 x 1.90
