svenpetersen1965/C64-Diagnostic-Rev.-586220-Harness/Diag586220_Harness/Case_3D_Data/User Port/Rev. 2 (SX-64)/User Port SX64/stl/diag_up_top_SX-64.stl

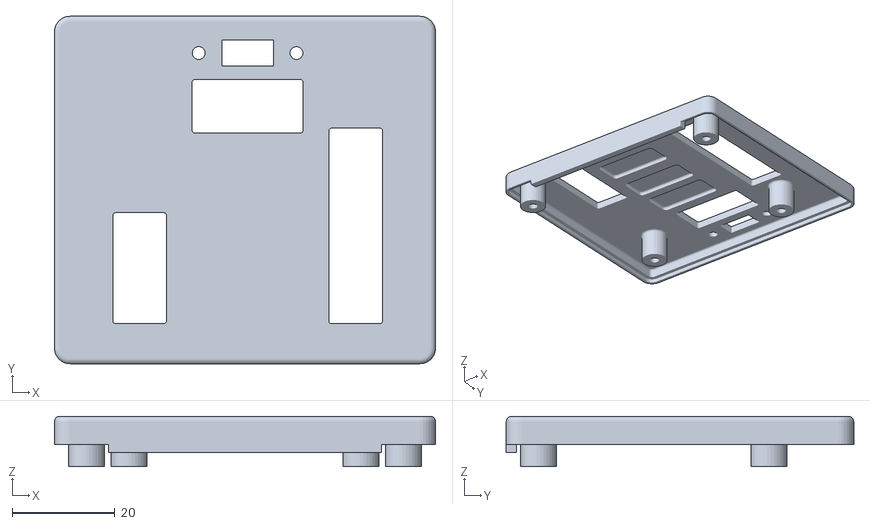
[picture p131: CAD file, 2020-08-10]
Diag586220_Harness/Case_3D_Data/User Port/Rev. 2 (SX-64)/User Port SX64/stl/diag_up_top_SX-64.stl
74.0 x 67.5 x 9.80
