svenpetersen1965/C64-Diagnostic-Rev.-586220-Harness/Diag586220_Harness/Case_3D_Data/User Port/Rev. 0/stl/bottom shell UP.stl

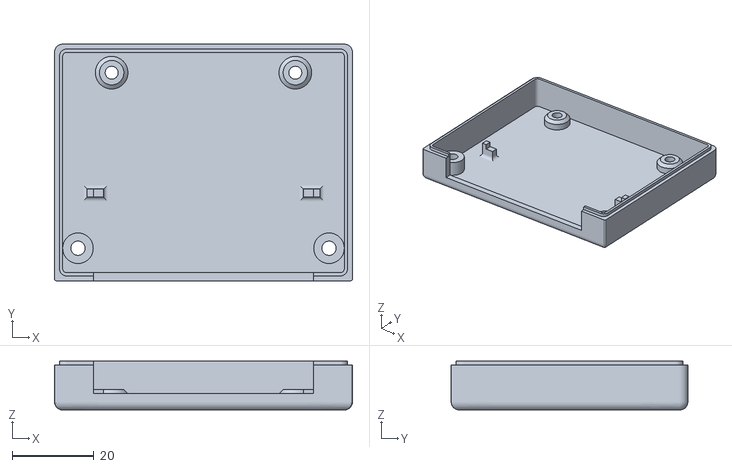
[picture p132: CAD file, 2019-09-12]
Diag586220_Harness/Case_3D_Data/User Port/Rev. 0/stl/bottom shell UP.stl
73.0 x 58.0 x 12.0
