svenpetersen1965/C64-Diagnostic-Rev.-586220-Harness/Diag586220_Harness/Case_3D_Data/User Port/Rev. 3/STL/diag_up_bottom.stl

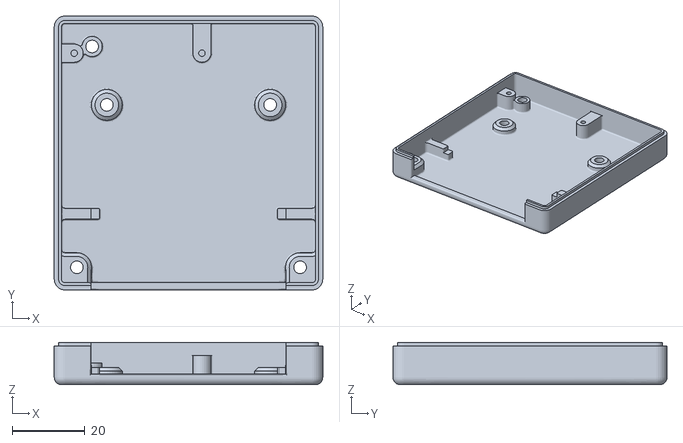
[picture p134: CAD file, 2022-08-29]
Diag586220_Harness/Case_3D_Data/User Port/Rev. 3/STL/diag_up_bottom.stl
74.0 x 75.5 x 11.7
