svenpetersen1965/C64-Diagnostic-Rev.-586220-Harness/Diag586220_Harness/Diag586220_User_Port/Rev.3/pictures/1333_-_Testing the 3digit VM.JPG

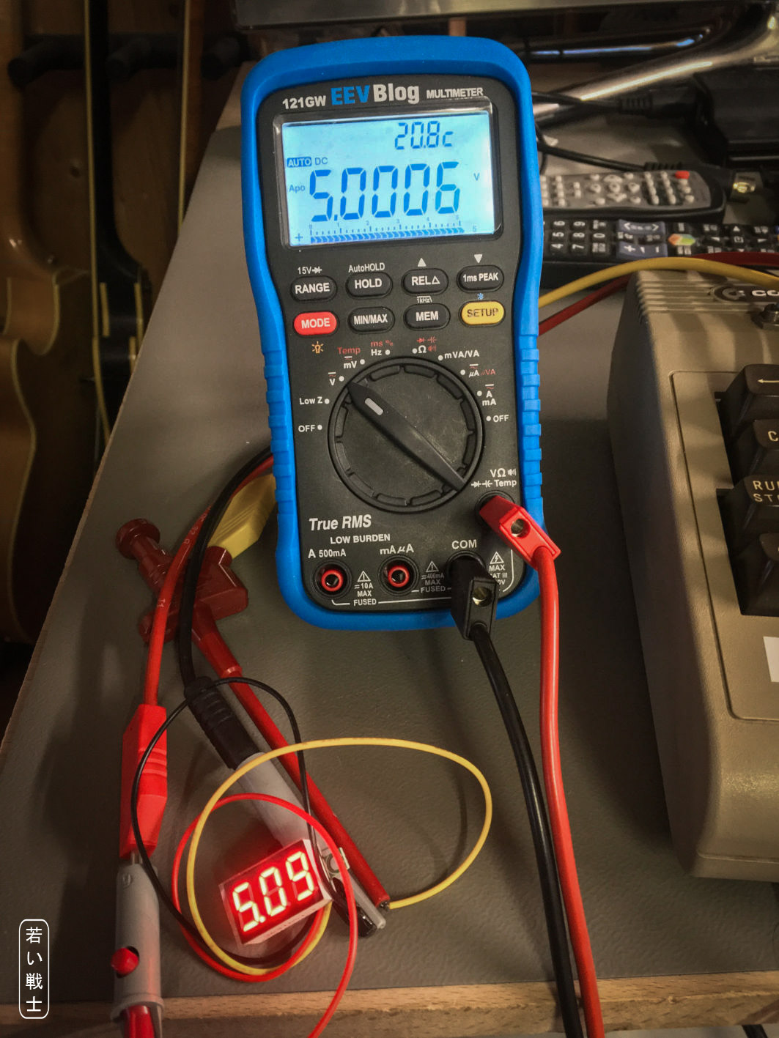
Diag586220_Harness/Diag586220_User_Port/Rev.3/pictures/1333_-_Testing the 3digit VM.JPG
