svenpetersen1965/C64-Diagnostic-Rev.-586220-Harness/Diag586220_Harness/Diag586220_User_Port/Rev.3/pdf/UP-CASP.pdf

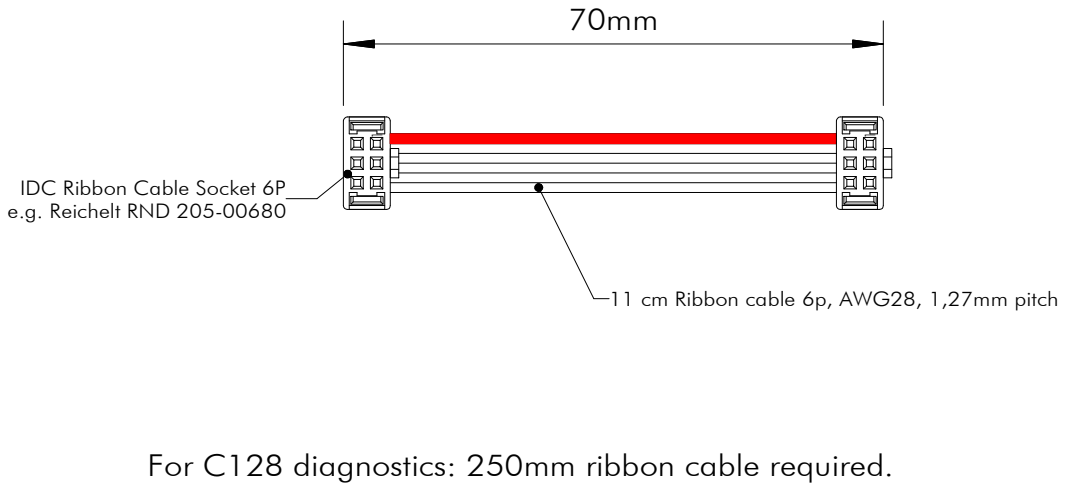
[picture p200: page 1]
Titel:; Doc.-No.: 113-3-01-01; Date: 08.06.2020 13:05; Diagnostic 586220 Harness

IDC Ribbon Cable Socket 6P
e.g. Reichelt RND 205-00680

11 cm Ribbon cable 6p, AWG28, 1,27mm pitch

For C128 diagnostics: 250mm ribbon cable required.

User Port - Cassette
Port Cable

Draft.: Sven Petersen
File:
Rev.: 1

UP-CASP.SKF
