svenpetersen1965/C64-Diagnostic-Rev.-586220-Harness/Diag586220_Harness/Diag586220_User_Port/Rev.3/pdf/UP-CTRLP.pdf

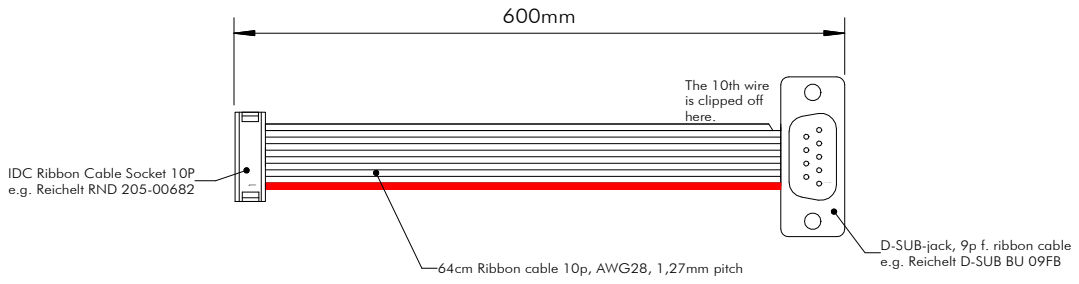
[picture p201: page 1]
Titel:; Doc.-No.: 113-3-02-01; Date: 08.06.2020 13:08; Diagnostic 586220 Harness

The 10th wire
is clipped off
here.

IDC Ribbon Cable Socket 10P
e.g. Reichelt RND 205-00682

D-SUB-jack, 9p f. ribbon cable
e.g. Reichelt D-SUB BU 09FB

64cm Ribbon cable 10p, AWG28, 1,27mm pitch

User Port - Control
Port Cable

Draft.: Sven Petersen
File:
Rev.: 1

UP-CTRLP.SKF
