svenpetersen1965/C64-Diagnostic-Rev.-586220-Harness/Diag586220_Harness/Diag586220_User_Port/Rev.3/pdf/UP-KEYB.pdf

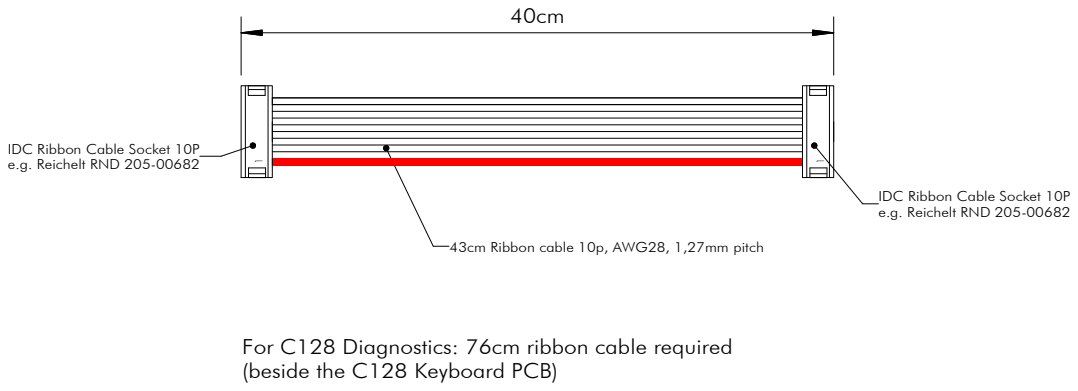
[picture p202: page 1]
Titel:; Doc.-No.: 113-3-04-01; Date: 08.06.2020 13:06; Diagnostic 586220 Harness

IDC Ribbon Cable Socket 10P
e.g. Reichelt RND 205-00682

43cm Ribbon cable 10p, AWG28, 1,27mm pitch

For C128 Diagnostics: 76cm ribbon cable required
(beside the C128 Keyboard PCB)

User Port - Keyboard
PCB Cable

Draft.: Sven Petersen
File:
UP-KEYB.SKF
Rev.: 1
