svenpetersen1965/C64-Diagnostic-Rev.-586220-Harness/Diag586220_Harness/C128_Keyboard_PCB/Rev. 0/pdf/C128_Diag_KB_v0.pdf

# Project Documentation

## C128 Diagnostic – Keyboard PCB

## Project number: 145

## Revision: 0

## Date: 27.04.2020

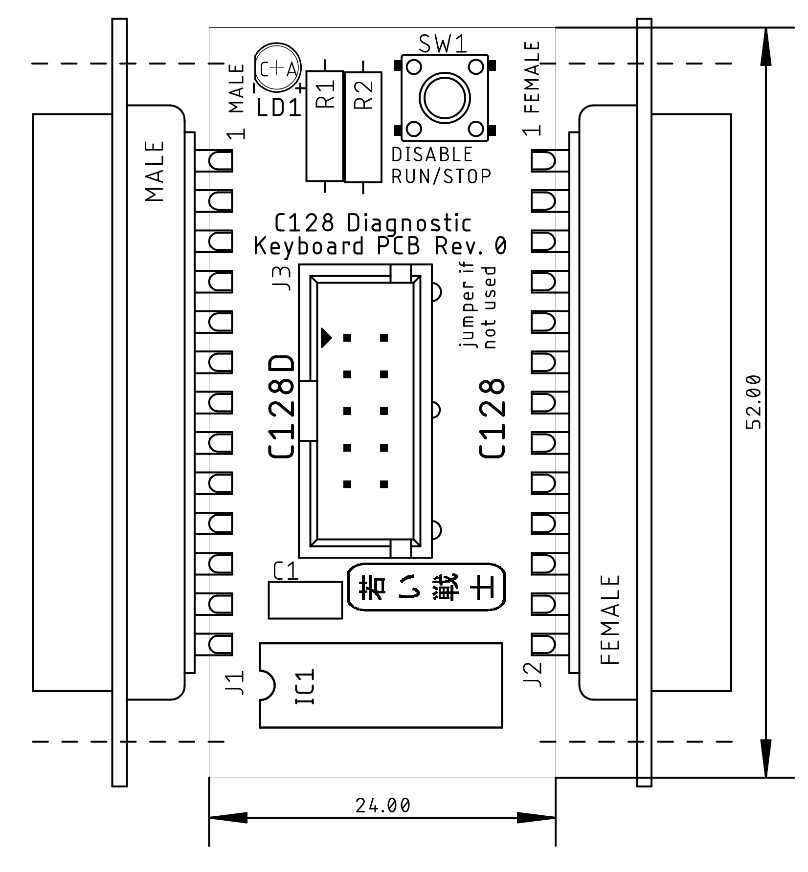
[picture p203: figure]

C128_Diag_KB_ModD.docx | | 27.04.2020 14:58
Drafted by Sven Petersen | Page 1 of 3 | Doc.-No.: 145-6-01-00

### C128 Diagnostic – Keyboard PCB Rev. 0

### Module Description

## Introduction

This is the keyboard Dongle (PCB) for the Commodore C128 Diagnostic Rev. 588121. The required harness is identical to the C64 Diagnostic Rev. 586220 harness, except the keyboard PCB. The C64 harness can be found here:

https://github.com/svenpetersen1965/C64-Diagnostic-Rev.-586220-Harness
A part of the keyboard scan lines are shared with the control ports. To prevent a false “OK”
while testing these, the feedbacks can be opened. The required analog switches are implemented on the user port PCB (Rev. 1) of the said C64 harness. The connection to the user port PCB is provided by a ribbon cable, which can be connected to the box pin header J3.

In case this feature is not desired or the user port PCB is of an earlier revision, the adjacent pins of J3 can be jumpered with standard jumpers (1-2, 3-4, 5-6, 7-8 and 9-10).

Figure 1: Dimensions of the C128 Diagnostic Keyboard PCB

The footprint of the keyboard connector on the C128 mainboard is for a 90° female DSub-25 connector (for the C128D). A special pin header is populated on the mainboard. It fits a female DSub-25 connector (J2). The pin numbering is in the opposite direction of a normal male DSub-25, though. This results in a discrepancy of the pin numbering of J2, which is correct.
The regular feedbacks are COL0 to ROW0, COL1 to ROW1, … COL7 to ROW7.

C128_Diag_KB_ModD.docx | | 27.04.2020 14:58
Drafted by Sven Petersen | Page 2 of 3 | Doc.-No.: 145-6-01-00

The feedback COL7 to ROW7 mimics a RUN/STOP while power up. This causes the C128 to boot into the monitor program, which is not desired. This can be circumvented by pressing the disable button on this PCB. This causes the analog switch (IC1) to open, which is responsible for this feedback.

## Connectors

Signal | J1 (C128D) | J2 (C128)
GND | 1 | 13
(no pin) | 2 | 12
RESTORE | 3 | 11
+5V | 4 | 10
ROW3 | 5 | 9
ROW6 | 6 | 8
ROW5 | 7 | 7
ROW4 | 8 | 6
ROW7 | 9 | 5
ROW2 | 10 | 4
ROW1 | 11 | 3
ROW0 | 12 | 2
COL0 | 13 | 1
COL6 | 14 | 25
COL5 | 15 | 24
COL4 | 16 | 23
COL3 | 17 | 22
COL2 | 18 | 21
COL1 | 19 | 20
COL7 | 20 | 19
K0 | 21 | 18
K1 | 22 | 17
K2 | 23 | 16
40/80 | 24 | 15
CAPS LOCK | 25 | 14

J3 – box pin header 2x5 circuits

Signal Pin | Pin Signal
COL4 | 1 | 2 | ROW4
COL3 | 3 | 4 | ROW3
COL2 | 5 | 6 | ROW2
COL1 | 7 | 8 | ROW1
COL0 | 9 | 10 | ROW0

C128_Diag_KB_ModD.docx | | 27.04.2020 14:58
Drafted by Sven Petersen | Page 3 of 3 | Doc.-No.: 145-6-01-00

## Links

This PCB is designed based on the following information:

- http://blog.worldofjani.com/?p=164
- http://personalpages.tds.net/~rcarlsen/cbm/c128/SCHEMATICS/
- https://commons.wikimedia.org/wiki/File:C128mobo.jpg?uselang=de

## Revision History

### Rev. 0

Prototype

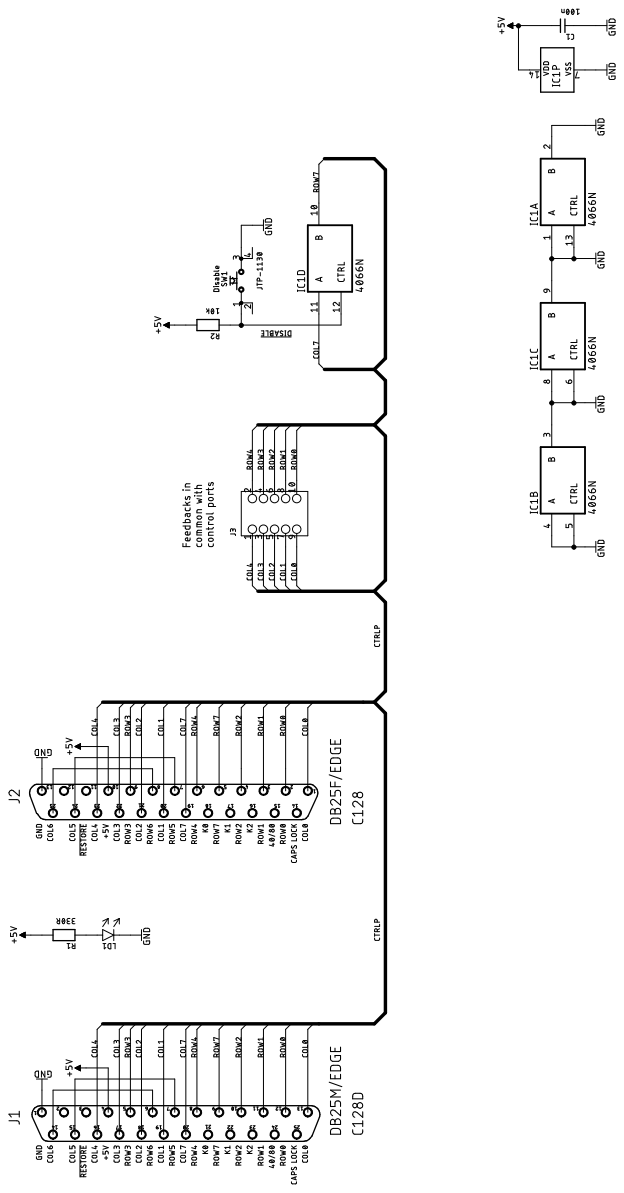
[picture p204: page 5]

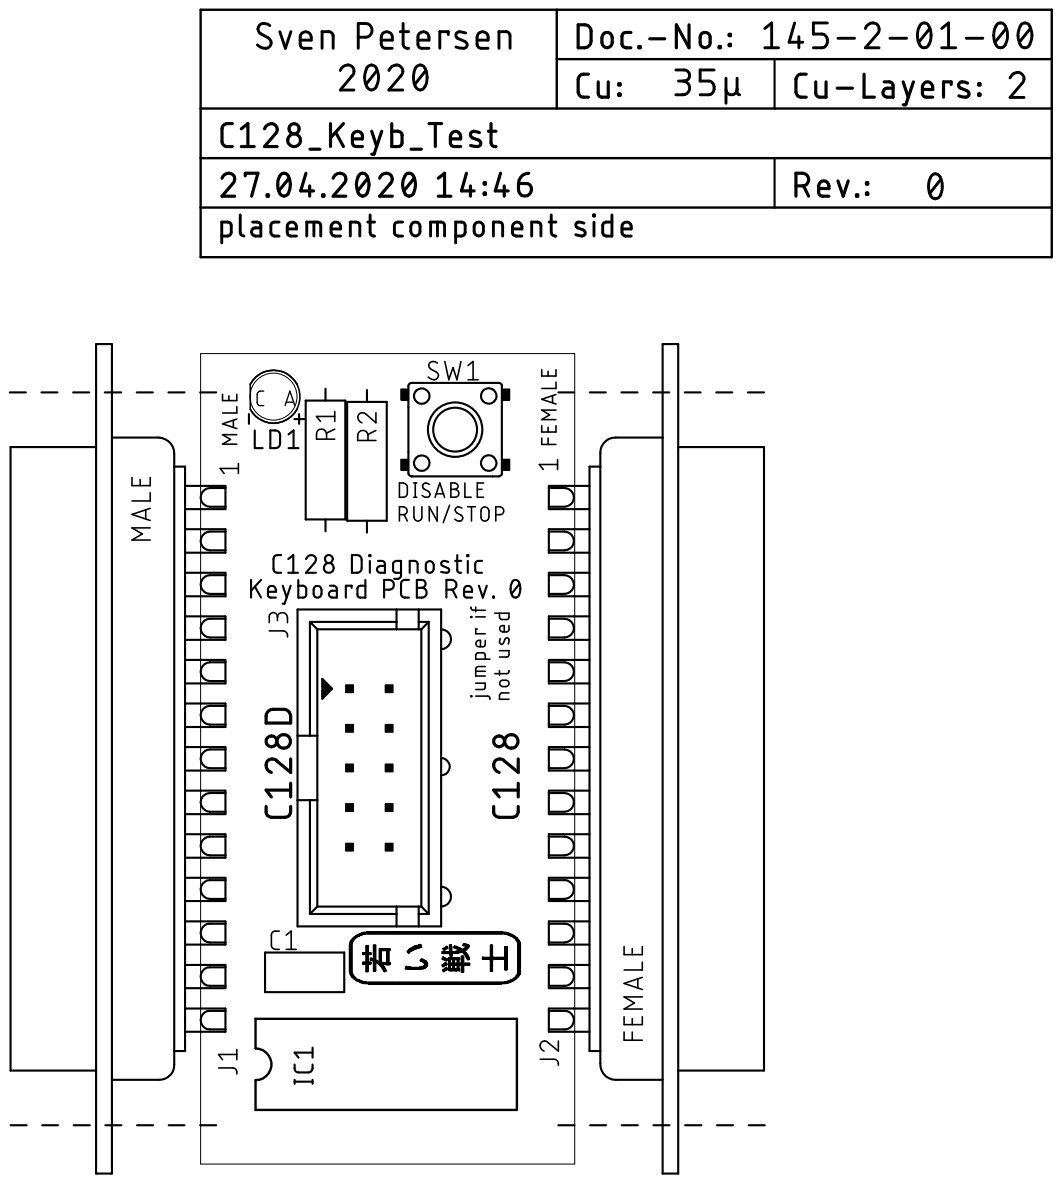
[picture p205: page 6]

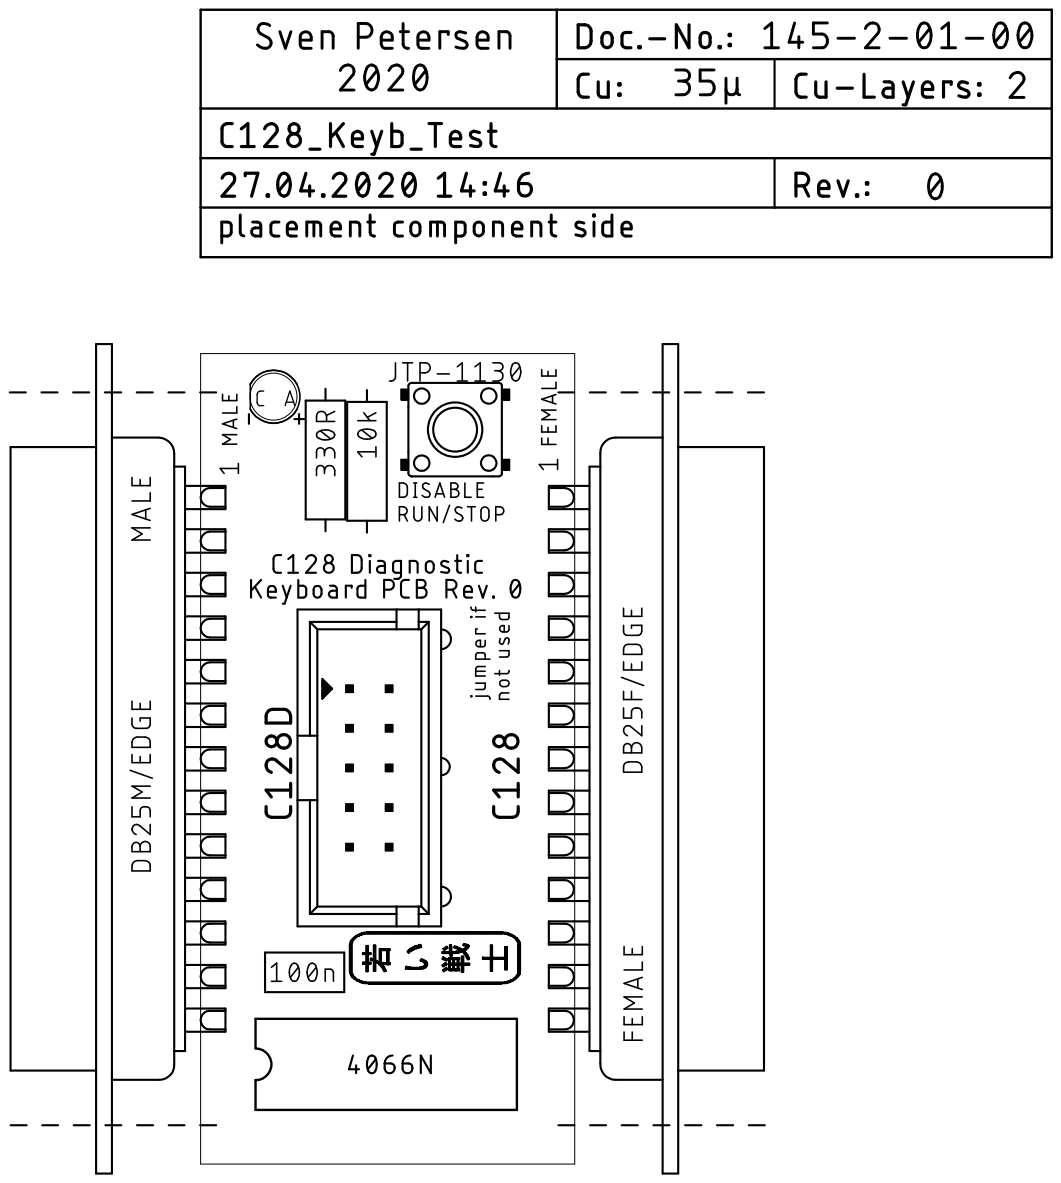
[picture p206: page 7]

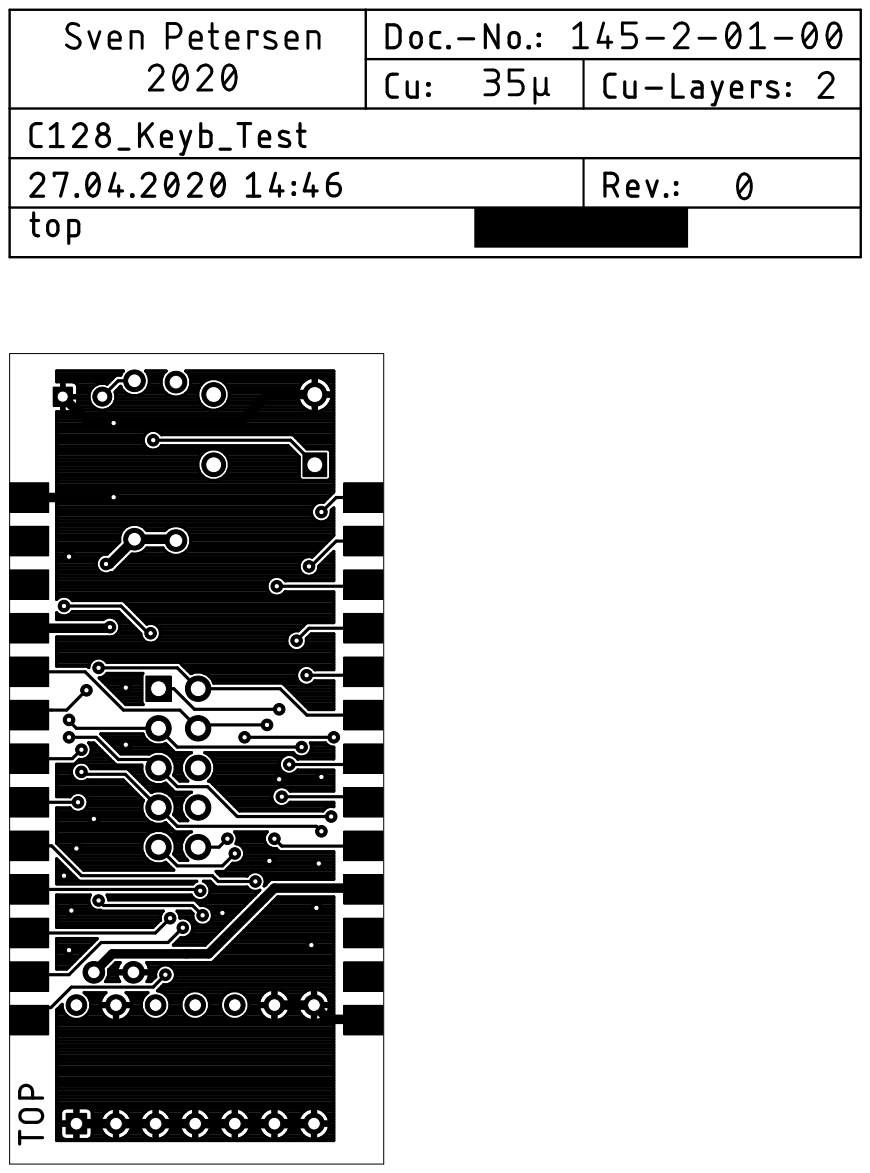
[picture p207: page 8]

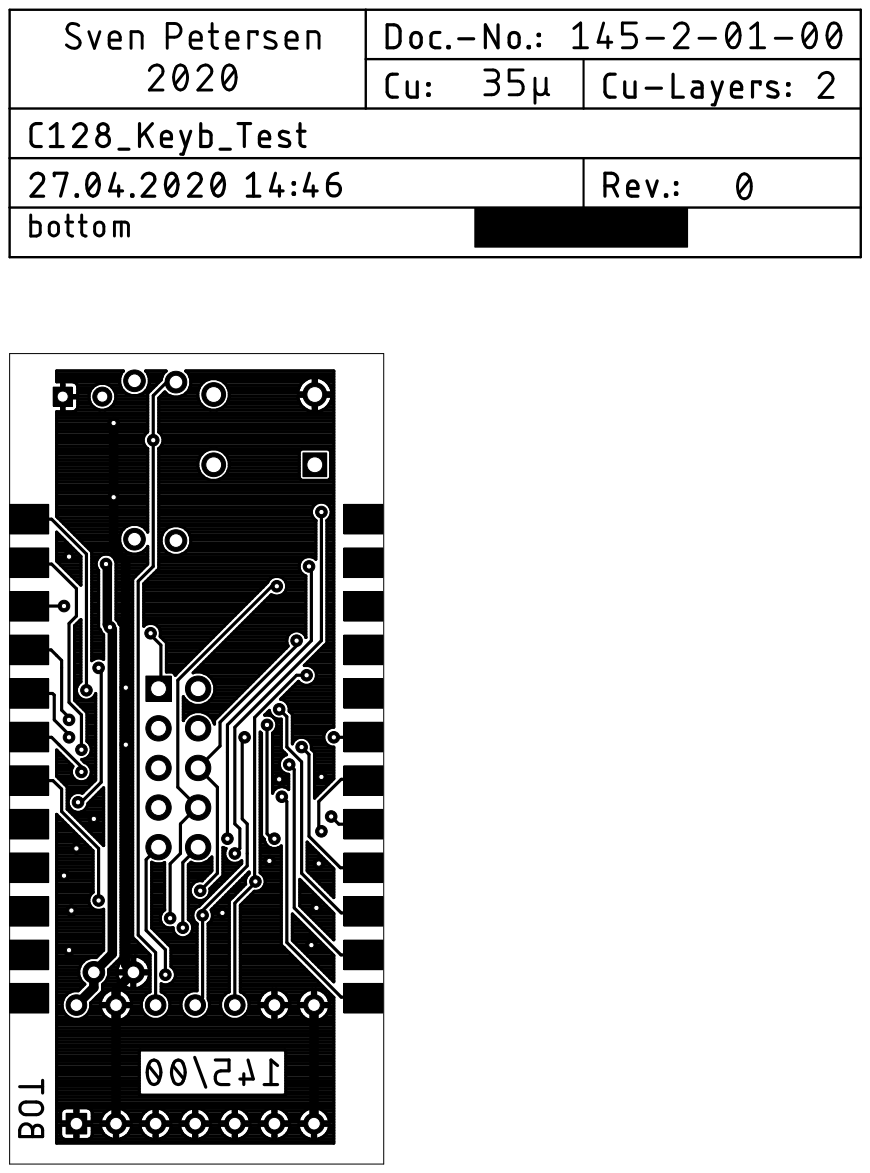
[picture p208: page 9]

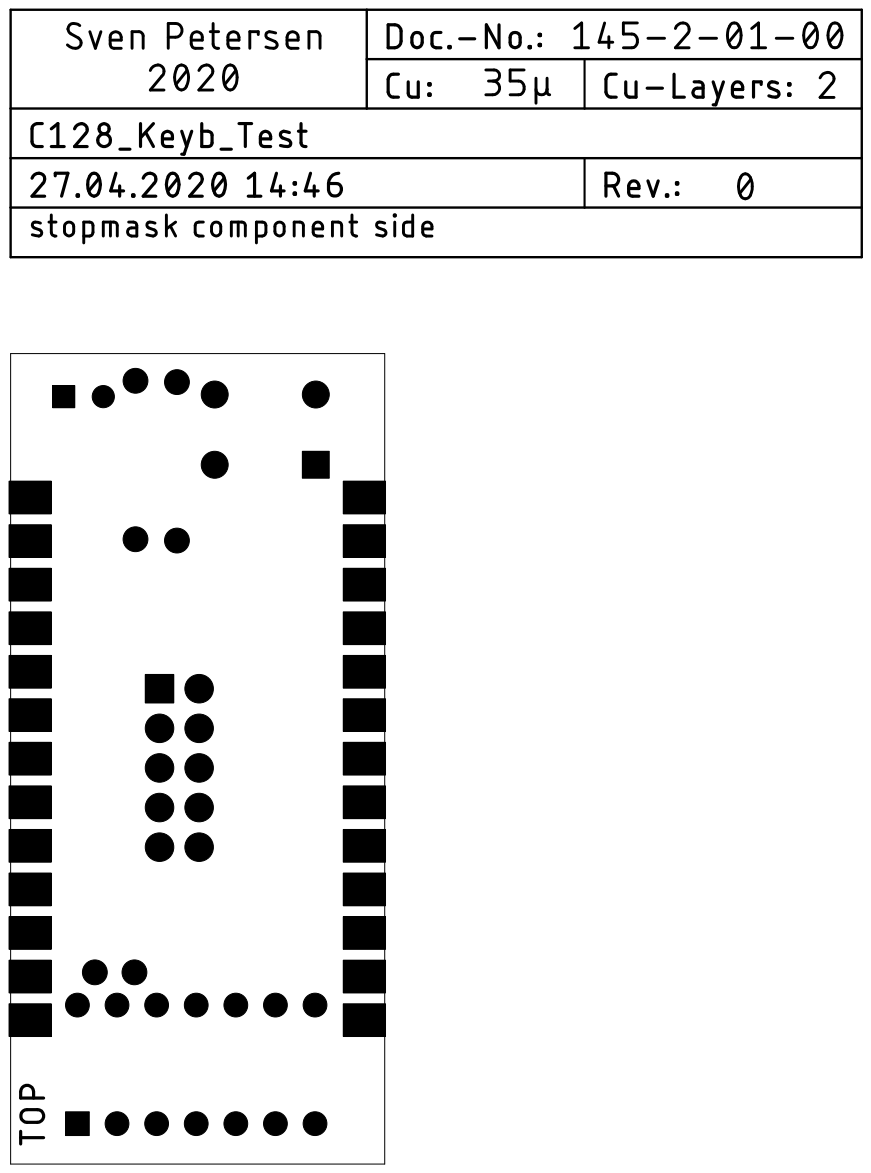
[picture p209: page 10]

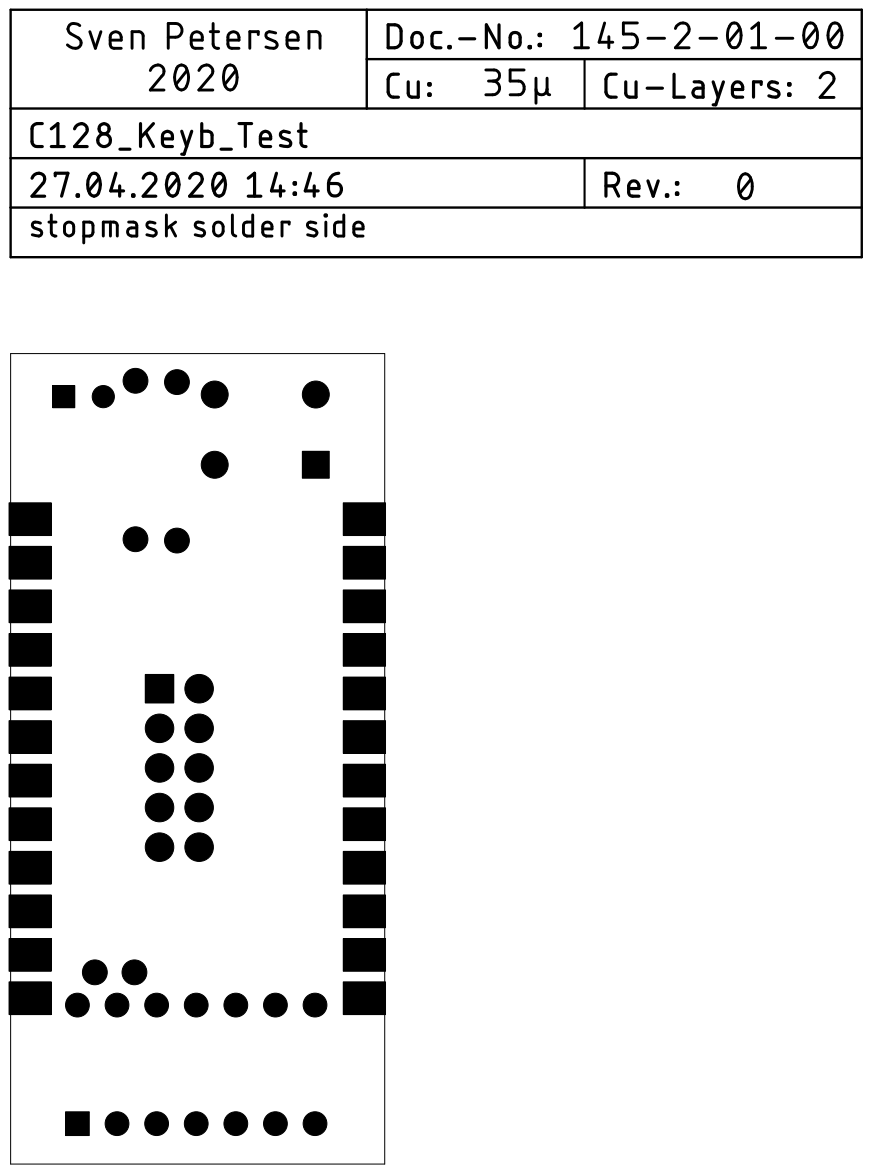
[picture p210: page 11]

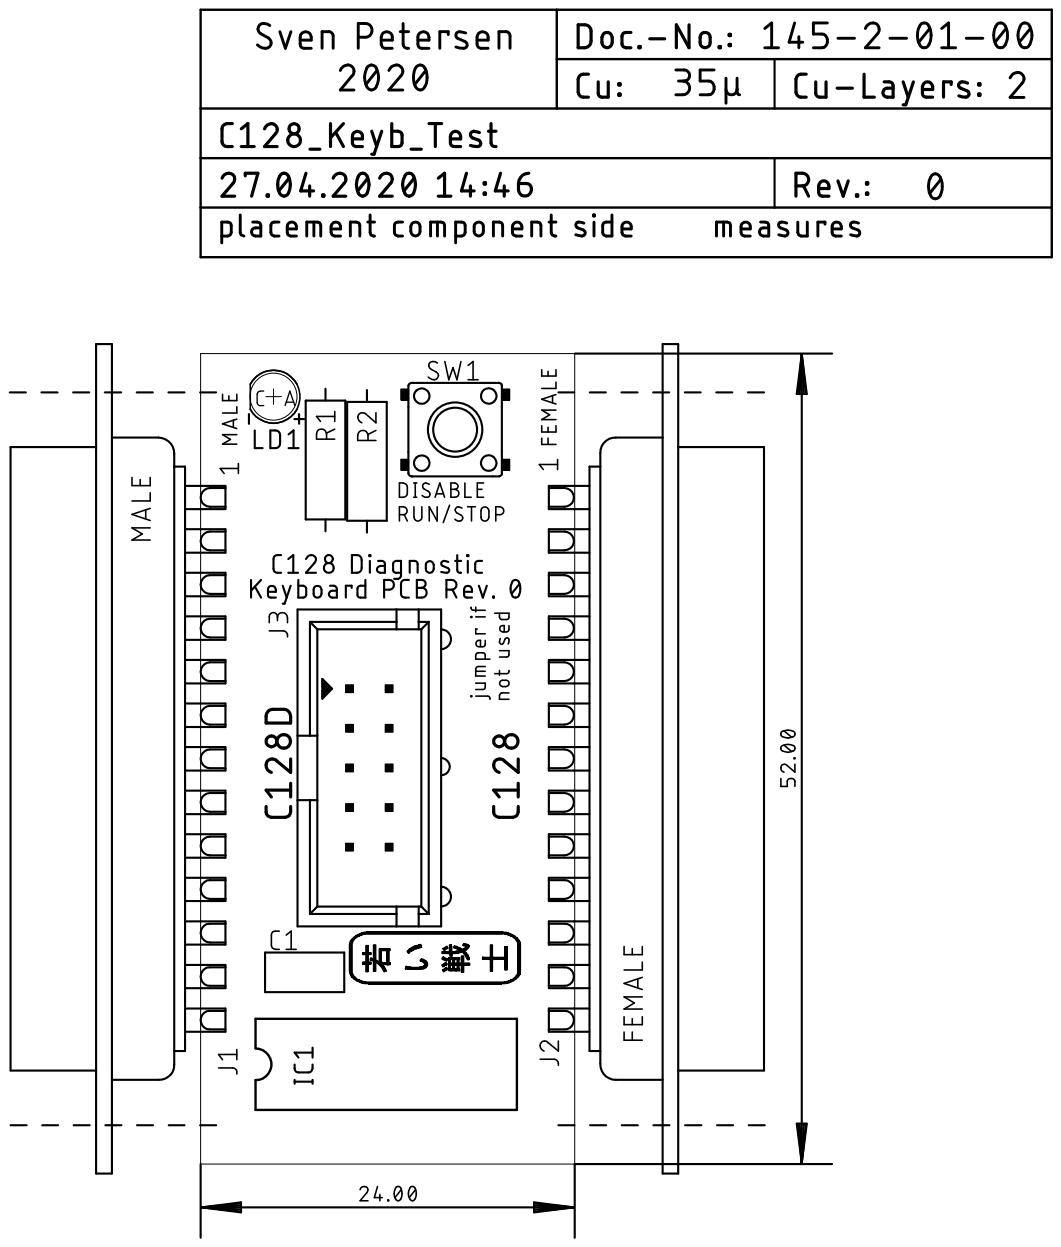
[picture p211: page 12]

Pos. Qty Value Footprint Ref.-No. Comment

1 1 145-2-01-00 2 Layer PCB Rev. 0 2 layer, Cu 35µ, HASL, 24.0 x 48.0mm, 1.6mm FR4

2 1 2x5pin box header,

2.54mm pitch

2X05WV J3 e.g. Reichelt.de: WSL 10G.

3 1 LED 3mm, green 3MM LD1 LED, standard

4 1 330R R-10 R1 Resistor, 0.25W, 5% or better

5 1 DB25F/EDGE DB25F-EDGE J2 DSub 25, female, solder cups, e.g. Reichelt.de: D-SUB BU

25

6 1 DB25M/EDGE DB25M-EDGE J1 DSub 25, male, solder cups, e.g. Reichelt.de: D-SUB ST 25

7 1 10k R-10 R1 Resistor, 0.25W, 5% or better

8 1 JTP-1130 JTP-1130 SW2 Standard 6x6mm tact switch, e.g. Namae JTP-1130 or any

other

9 1 HCF4066B DIL14 IC1 ST Micro or equivalent (4066)

10 1 DIL 14 DIL14 (IC1) DIL IC sockets

11 1 100n/50V C-2,5 C1 cer. cap, 2.5mm pitch

## C128 Diagnostic Keyboard PCB Rev. 0

## Bill of Material Rev. 0.0

C128_Diag_KeyB_BOM_v0_0.xlsx

Drafted by Sven Petersen Page 1 of 1

27.04.2020 15:03
Doc.No.: 145-5-01-00.0
