svenpetersen1965/C64-Diagnostic-Rev.-586220-Harness/Diag586220_Harness/Diag586220_Keyboard_ext/Rev. 0/pictures/C64_Keyb-Test-ext.pdf

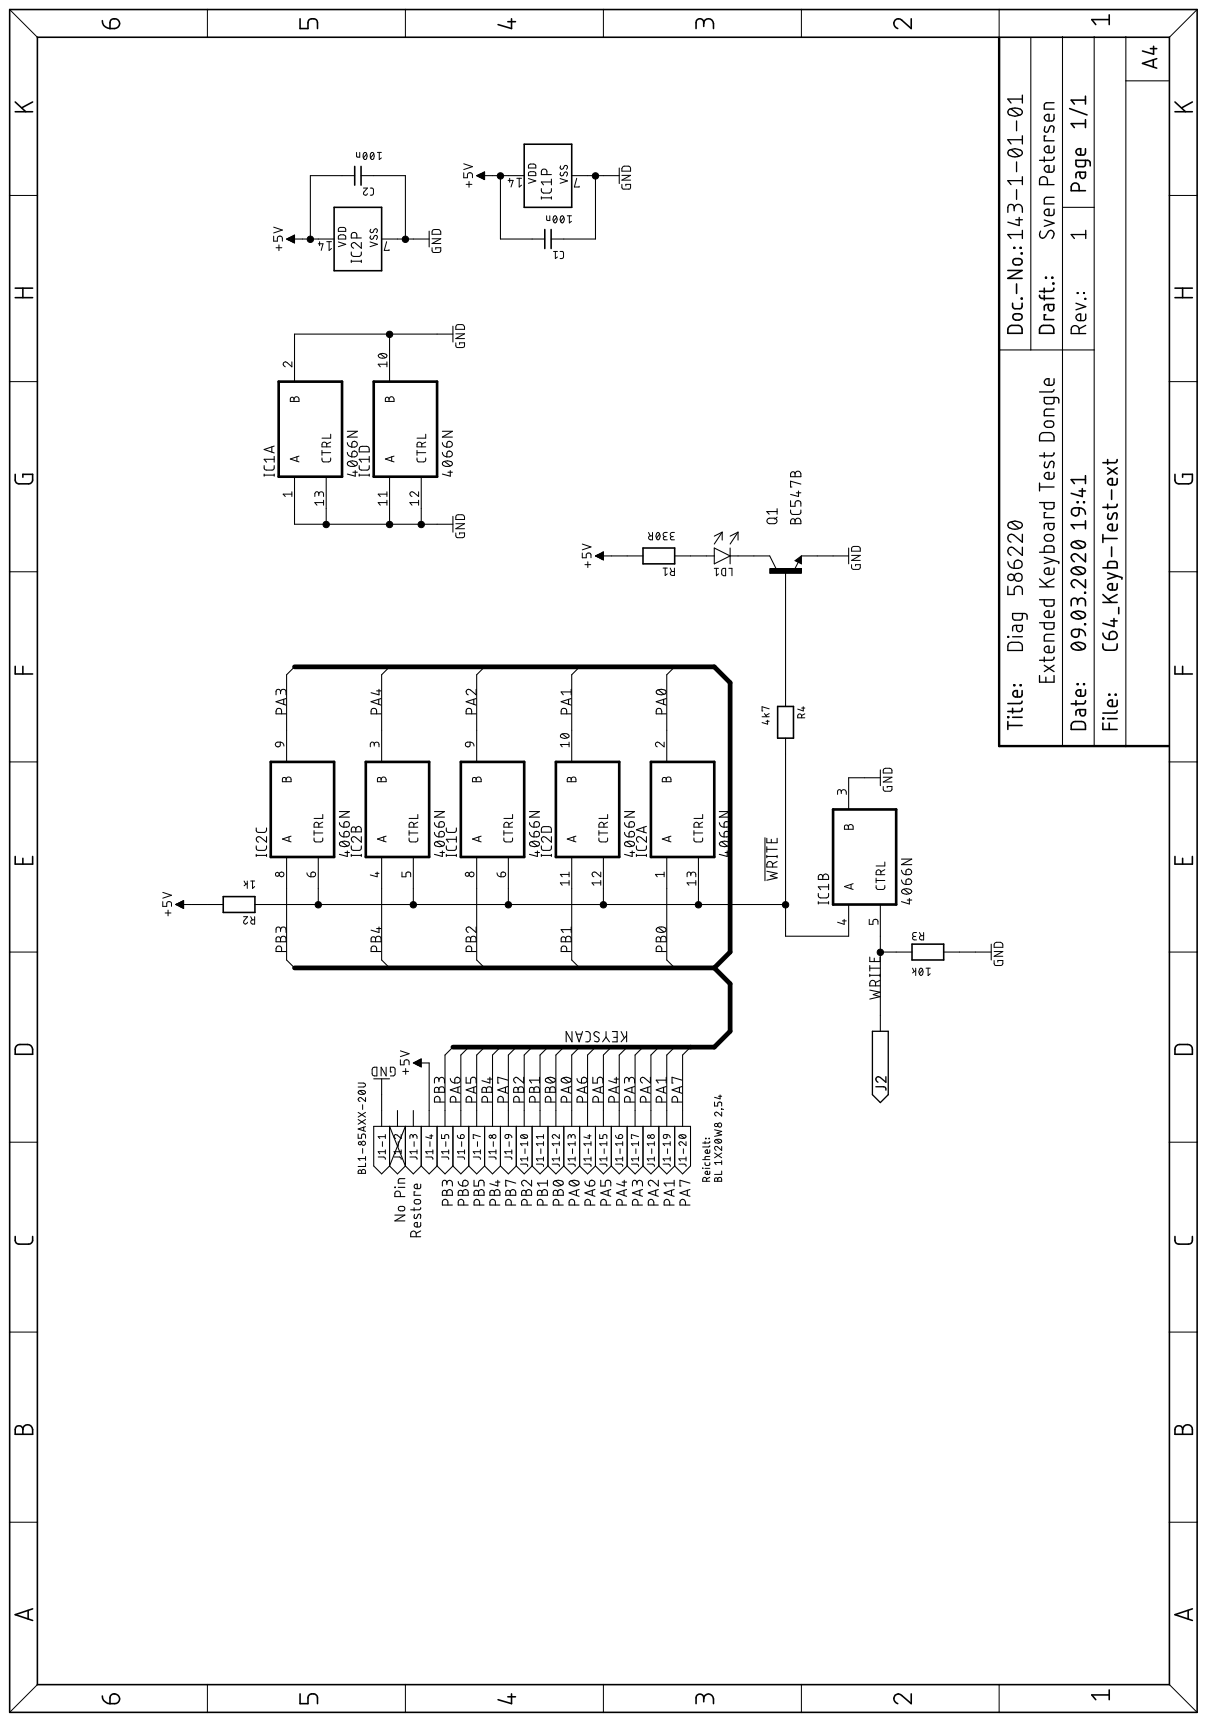
[picture p223: page 1]
