svenpetersen1965/C64-Diagnostic-Rev.-586220-Harness/Diag586220_Harness/Diag586220_User_Port/Rev.0/pdf/Diag586220_User_Port_v0.pdf

# Project Documentation

## Diagnostic Rev. 586220 Harness - User Port

## Project number: 113

## Revision: 0

## Date: 28.02.2019

Diag586220_User_Port_ModB.docx | | 14.02.2020 22:58
Drafted by Sven Petersen | Page 1 of 3 | Doc.-No.: 113-6-01-00

### Diagnostic Rev. 586220 Harness - User Port

### Module Description

The User Port module is the central part of the Diagnostic Rev. 586220 harness. It provides

### the required feedback connections for testing the C64’s CIA U2, which is connected to the

user port. It also holds the analog switches, which are required to test the Control Ports and the feedback connections for testing the cassette port.

The MOTOR output signal of the cassette port has approximately a 6V level. To use it as a
control signal for operating logic devices, a voltage divider consisting out of a 150Ω resistor
and a 320Ω (316Ω works here, 330Ω should work as well) resistor is required, which has a ratio of about 0.7.

This way, the MOTOR signal is fed back to the WRITE pin and is also used for switching the analog switches between the joystick signals of both control ports.

## Pin Outs

### User Port

J1- Edge Connector (2x12, 3.96mm pitch)

Pin Signal | Pin Signal
1 | GND | A | GND
2 | +5V | B | /FLAG2
3 | /RESET | C | PB0
4 | CNT1 | D | PB1
5 | SP1 | E | PB2
6 | CNT2 | F | PB3
7 | SP2 | H | PB4
8 | /PC2 | J | PB5
9 | ATN | K | PB6
10 | 9VAC(1) | L | PB7
11 | 9VAC(2) | M | PA2
12 | GND | N | GND

### Cassette Port

J2 – 2x3 pin header for a ribbon cable connected to the cassette port PCB (project number 114).

Pin Signal | Pin Signal
1 | GND | 2 | n.c.
3 | MOTOR | 4 | READ
5 | WRITE | 6 | SENSE

Diag586220_User_Port_ModB.docx | | 14.02.2020 22:58
Drafted by Sven Petersen | Page 2 of 3 | Doc.-No.: 113-6-01-00

### Control Port #1

J3 – 2x5 pin header for a ribbon cable which connects via a D-SUB 9 (female) to the control port.

Pin D-SUB Signal | Pin D-SUB Signal
1 | 1 | JOYA0 (up) | 2 | 6 | FIREA
3 | 2 | JOYA1 (down) | 4 | 7 | +5VCTR1
5 | 3 | JOYA2 (left) | 6 | 8 | n.c. (GND)
7 | 4 | JOYA3 (right) | 8 | 9 | POTXA
9 | 5 | POTYA | 10 | - | n.c.

### Control Port #2

J4 – 2x5 pin header for a ribbon cable which connects via a D-SUB 9 (female) to the control port.

Pin D-SUB Signal | Pin D-SUB Signal
1 | 1 | JOYB0 (up) | 2 | 6 | FIREB
3 | 2 | JOYB1 (down) | 4 | 7 | +5VCTR2
5 | 3 | JOYB2 (left) | 6 | 8 | n.c. (GND)
7 | 4 | JOYB3 (right) | 8 | 9 | POTXB
9 | 5 | POTYB | 10 | - | n.c.

## Interconnects

### User Port

Pin | Signal | Signal | Pin
4 | CNT1 | « | CNT2 | 6
5 | SP1 | « | SP2 | 7
8 | /PC2 | « | /FLAG2 | B
9 | ATN | « | PA2 | M
C | PB0 | « | PB4 | H
D | PB1 | « | PB5 | J
E | PB2 | « | PB6 | K
F | PB3 | « | PB7 | L

### Cassette Port

Pin | Signal | Signal Pin
3 | MOTOR | Volt.div. | WRITE | 5
4 | READ | « | SENSE | 6

Diag586220_User_Port_ModB.docx | | 14.02.2020 22:58
Drafted by Sven Petersen | Page 3 of 3 | Doc.-No.: 113-6-01-00

### Control Ports

Signal | Signal
FIREA | switched by MOTOR | FIREB
JOYA0 | switched by MOTOR | JOYB0
JOYA1 | switched by MOTOR | JOYB1
JOYA2 | switched by MOTOR | JOYB2
JOYA3 | switched by MOTOR | JOYB3
POTXA | via 110kΩ (R1) | +5V (CTR 1)
POTYA | via 110kΩ (R2) | +5V (CTR 1)
POTXB | via 110kΩ (R5) | +5V (CTR 2)
POTYB | via 110kΩ (R6) | +5V (CTR 2)

The digital signals of the control ports are connected by an analog switch. A HIGH level of the MOTOR signal will switch on.

The POT (paddle) signals are tested with a fix resistor of 110k, that is connected to the +5V provided by the respective control port.

## Cables

### User Port/Cassette Port Cable

One cable as shown in Doc.-No. 113-3-01-00 is required. It connects to J2.

### User Port/Control Cables

Two cables as shown in Doc.-Nr. 113-3-02-00 are required. They connect to J3 and J4.

### The IEC-Dongle

The IEC-Dongle is not attached to the PCB, it is an extra built.

6p. DIN plug, connect according to Doc.-No. 113-3-03-00

Pin | Signal | Signal Pin
1 | SRQ | « | DATA | 5
3 | ATN | « | CLK | 4

## Revision History

BOM v0.1 → v0.2

Pos. 6: value 120k →110k

Pos. 8: value 320R →316R

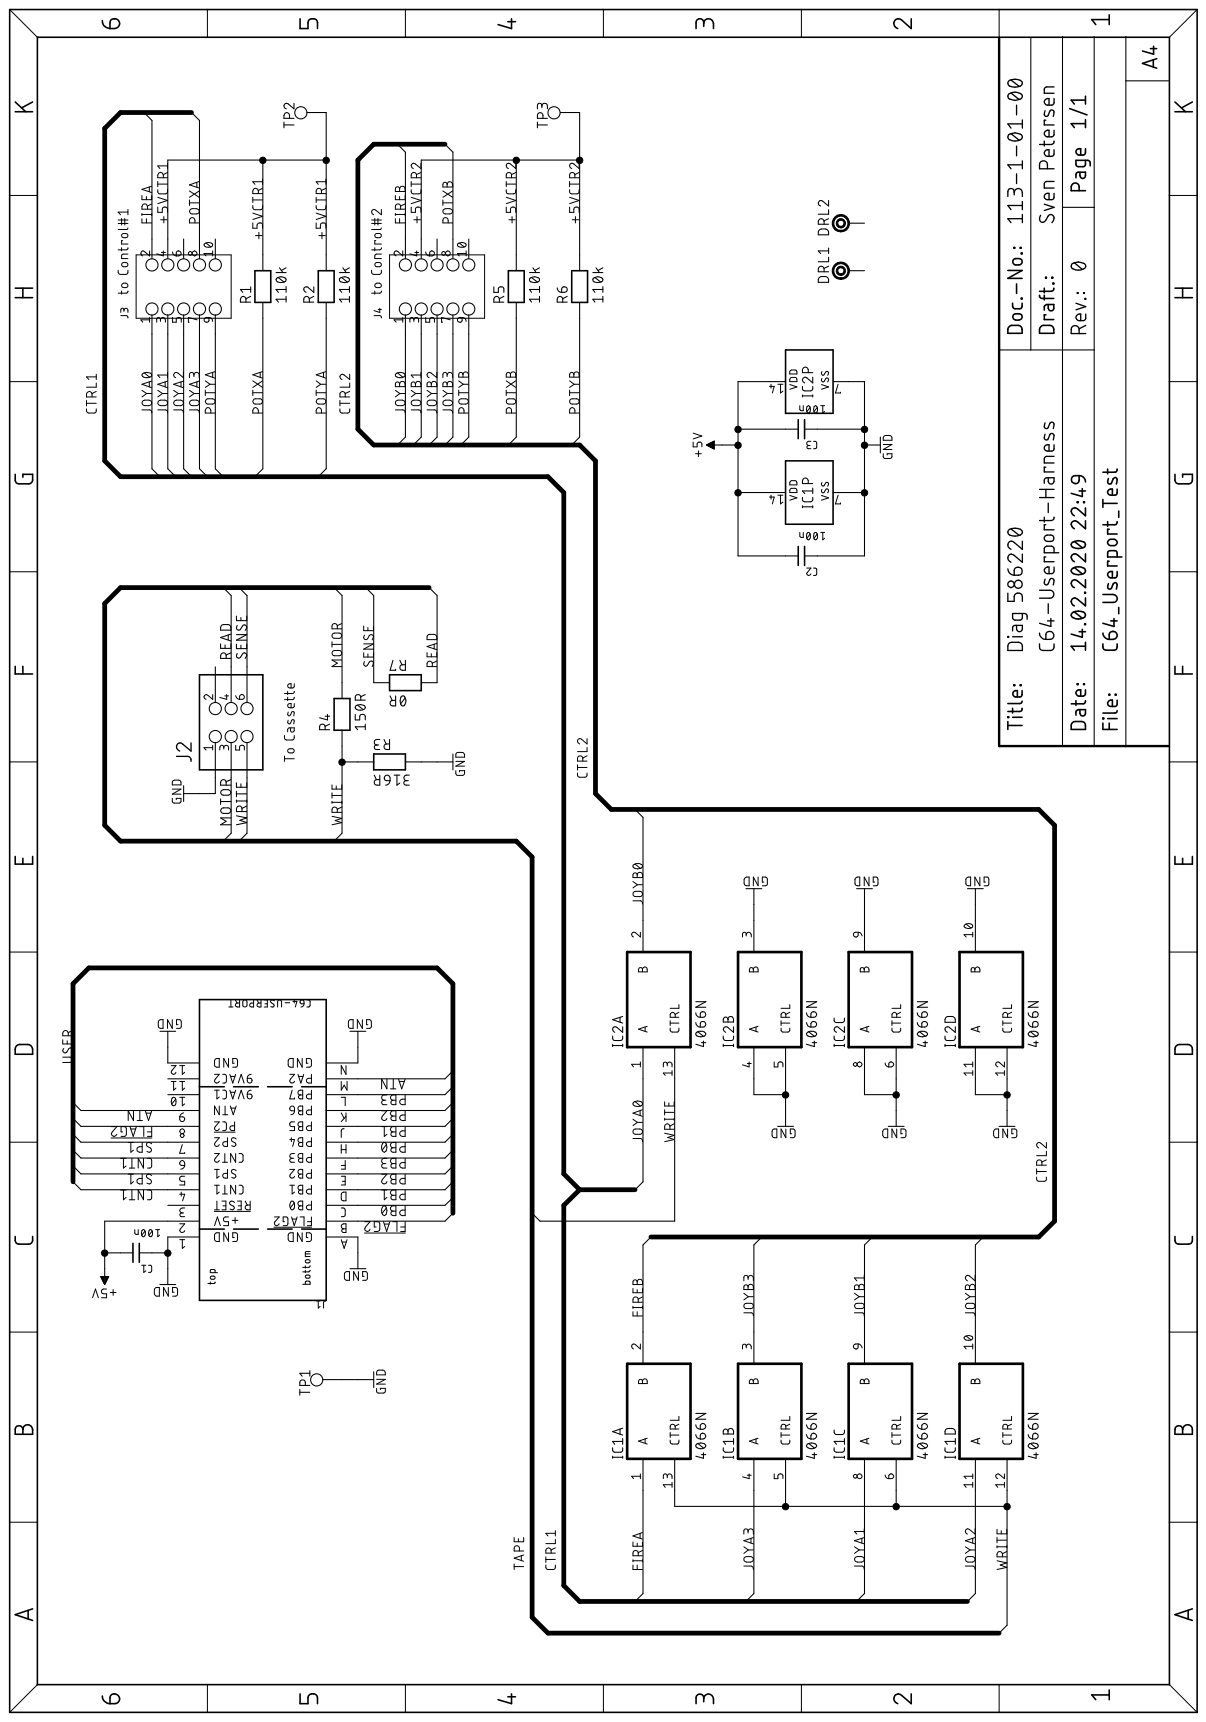
[picture p252: page 5]

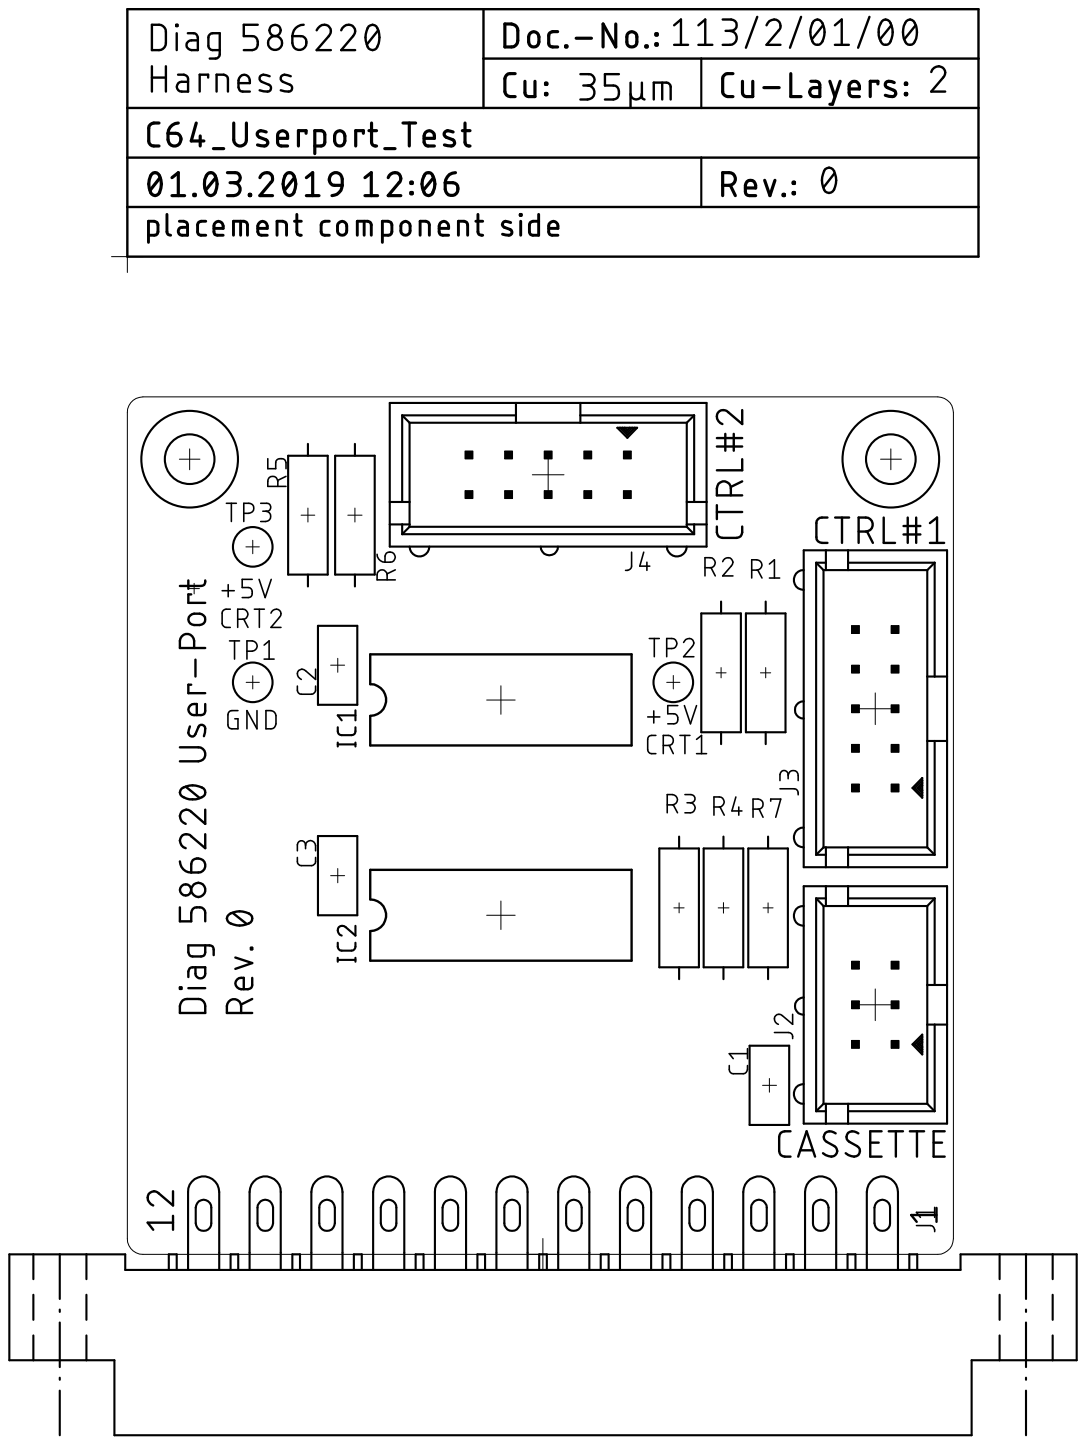
[picture p253: page 6]

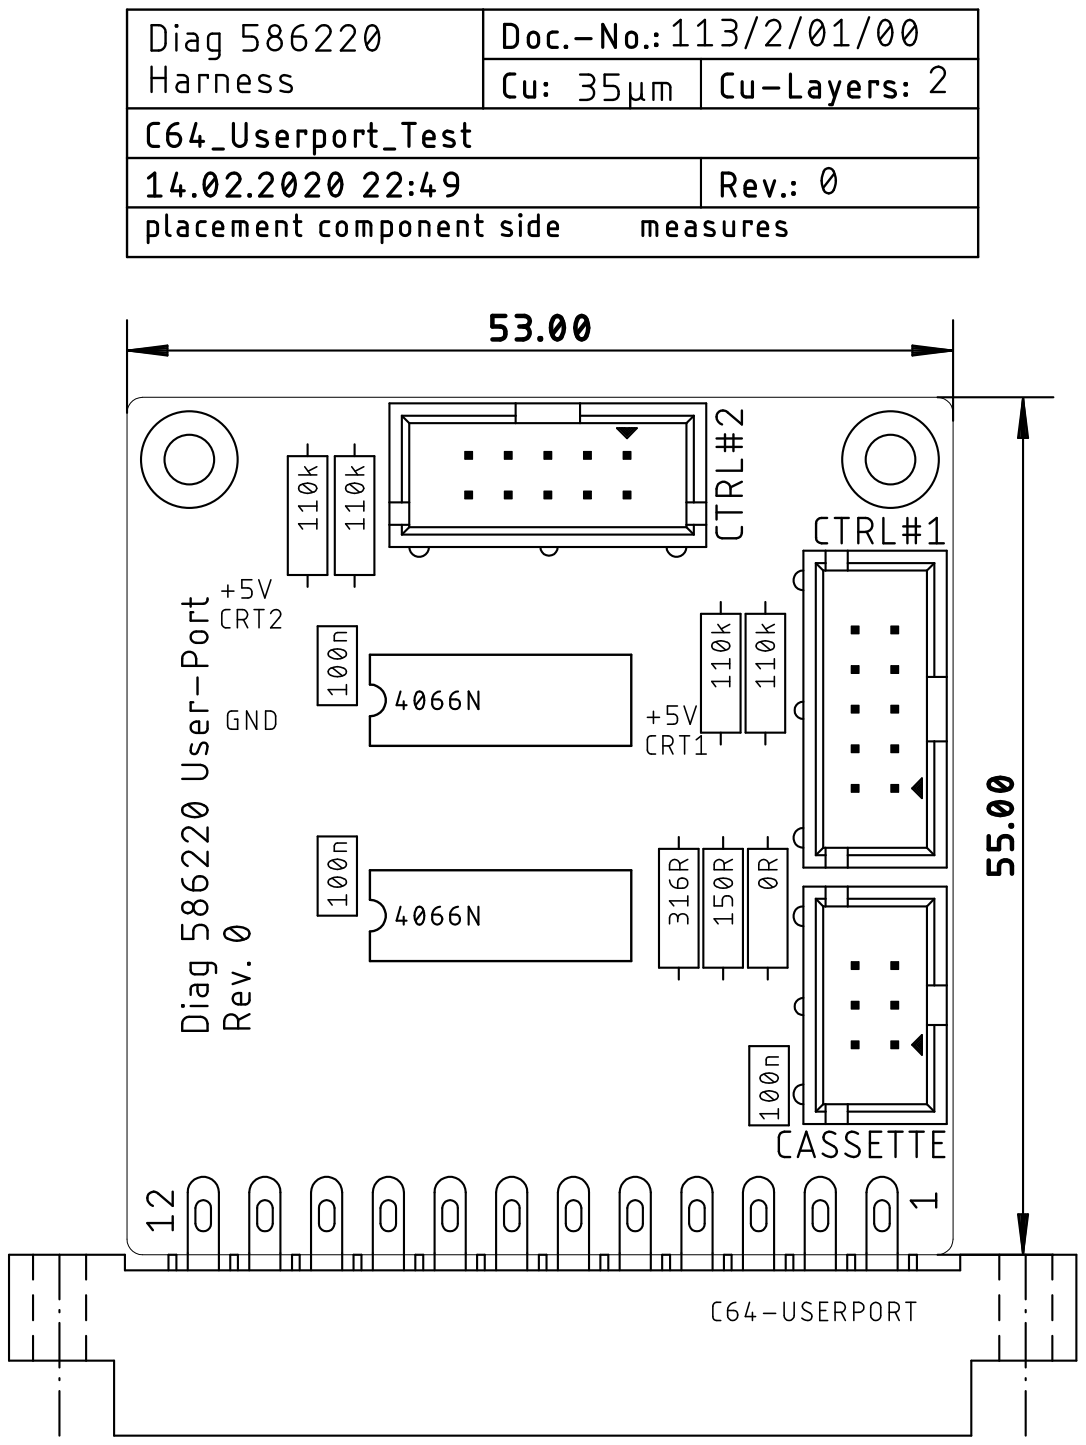
[picture p254: page 7]

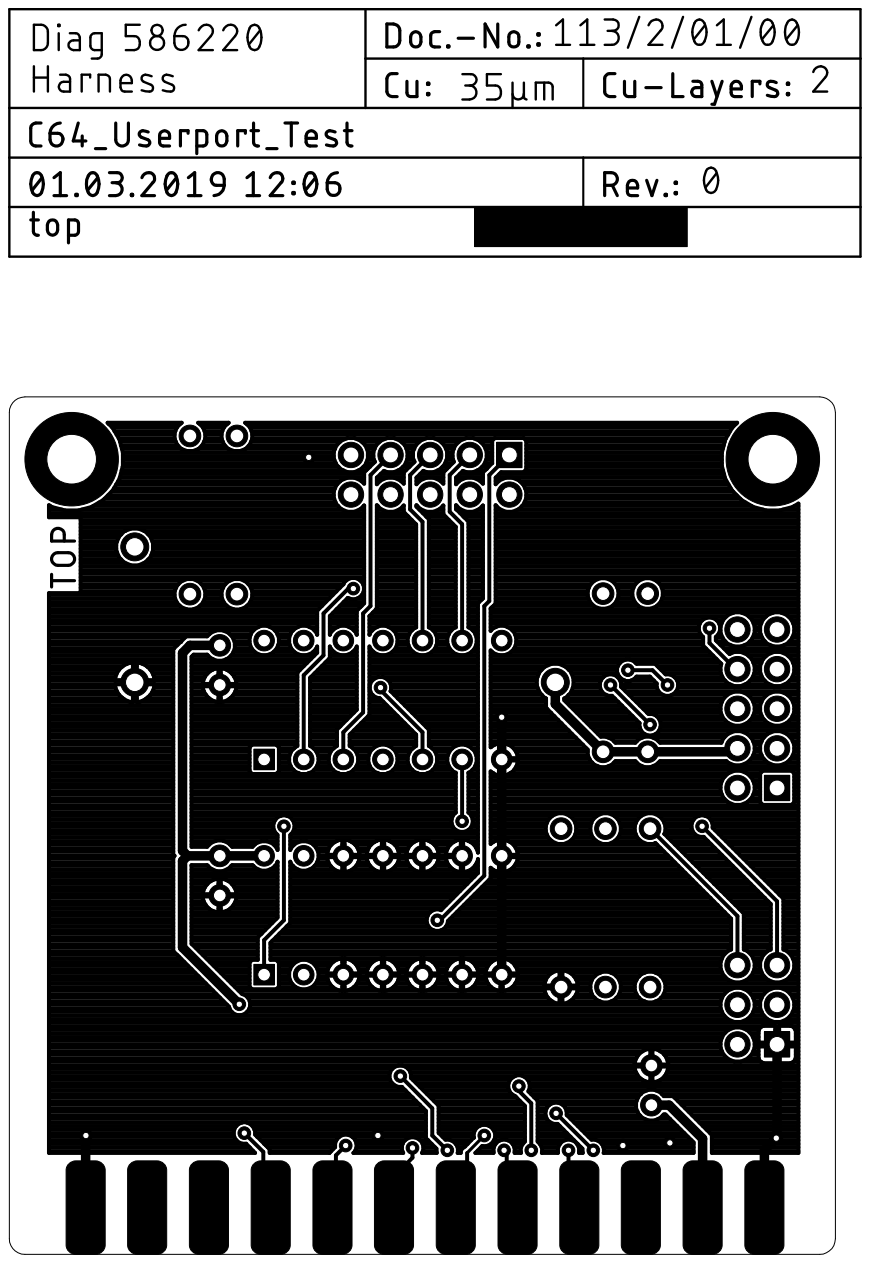
[picture p255: page 8]

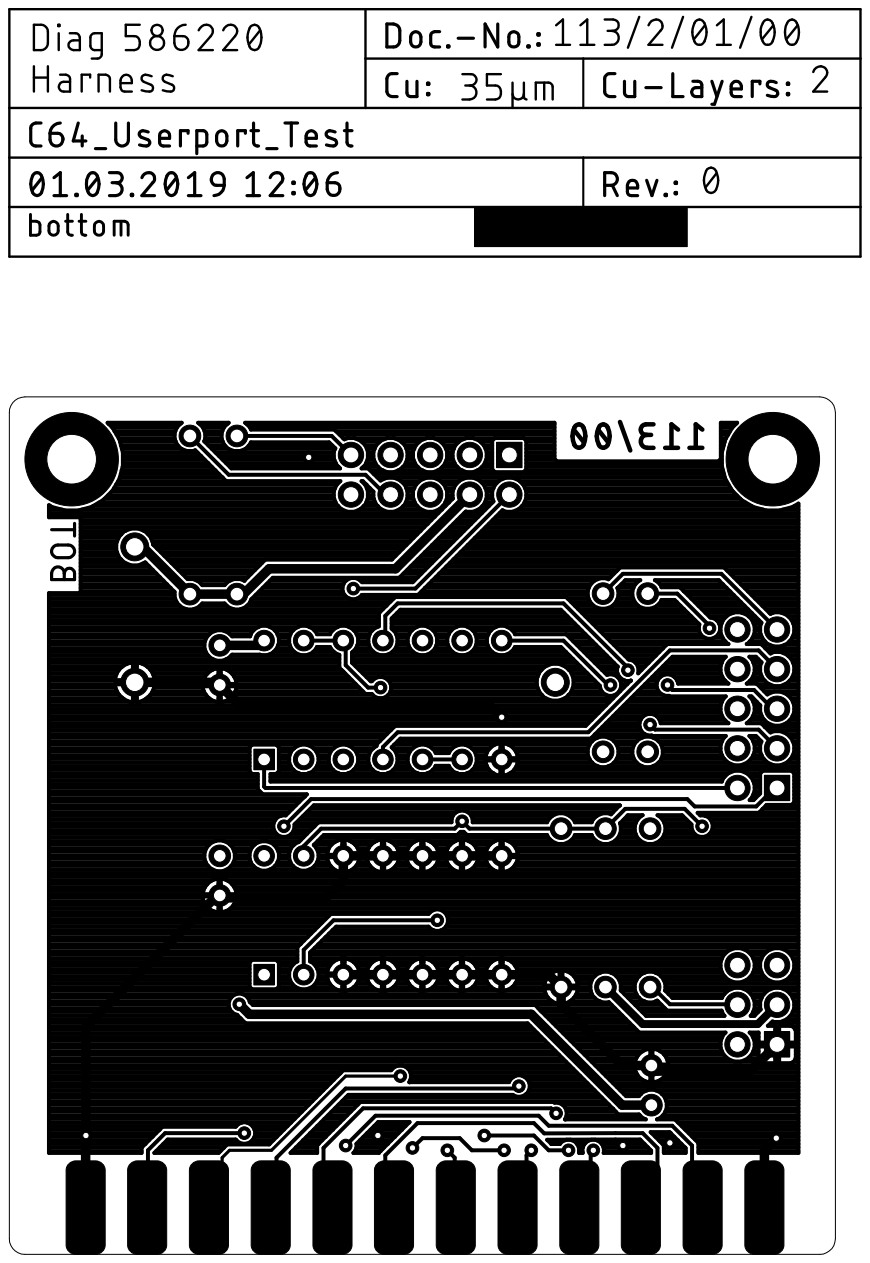
[picture p256: page 9]

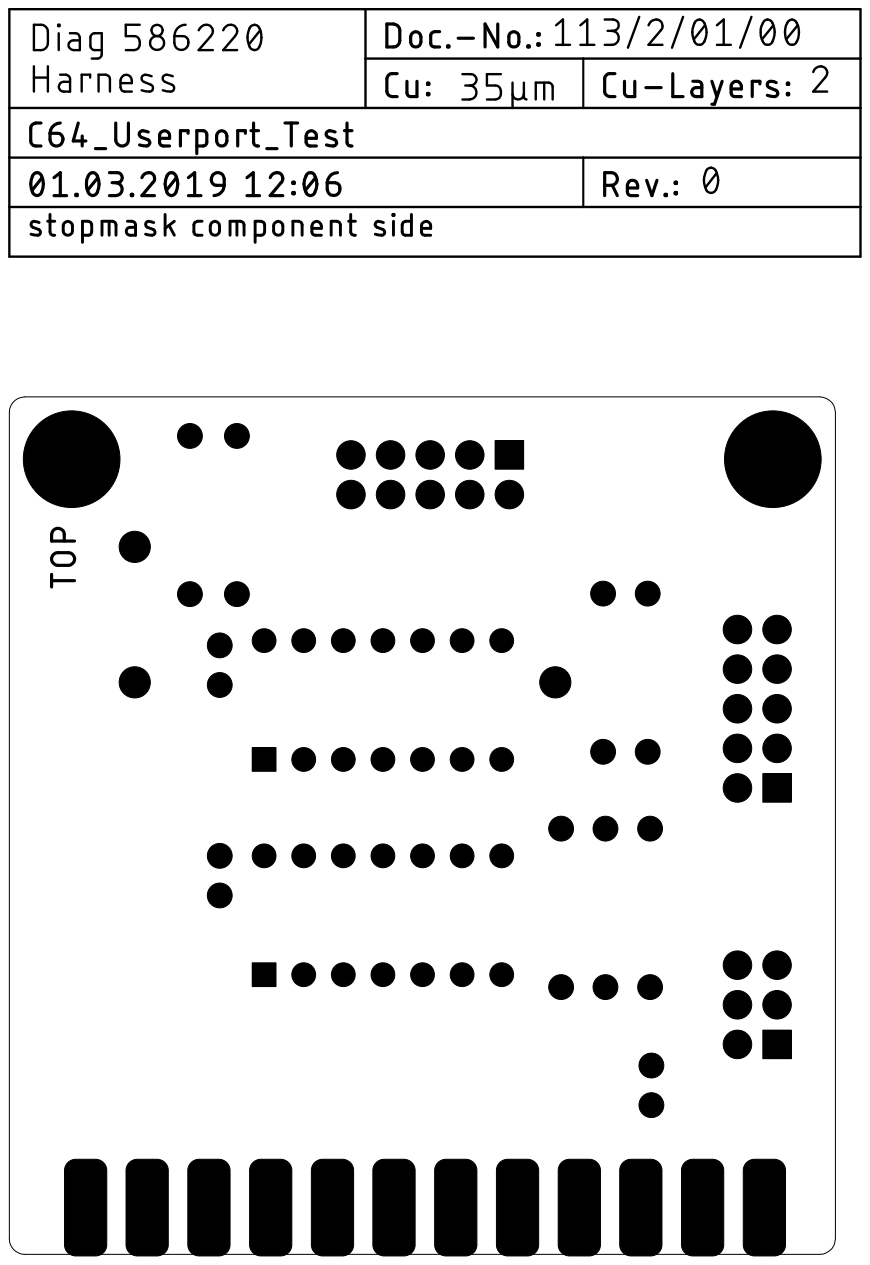
[picture p257: page 10]

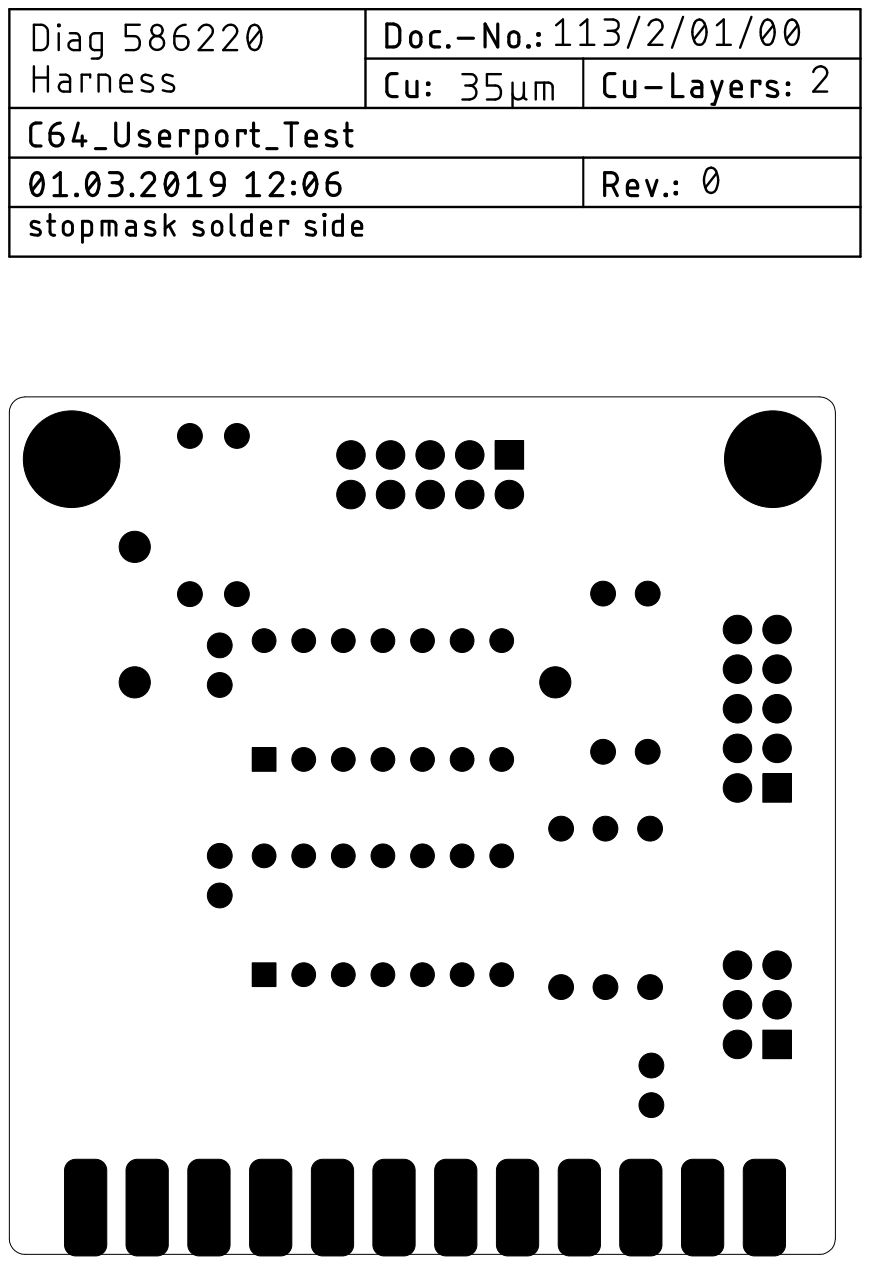
[picture p258: page 11]

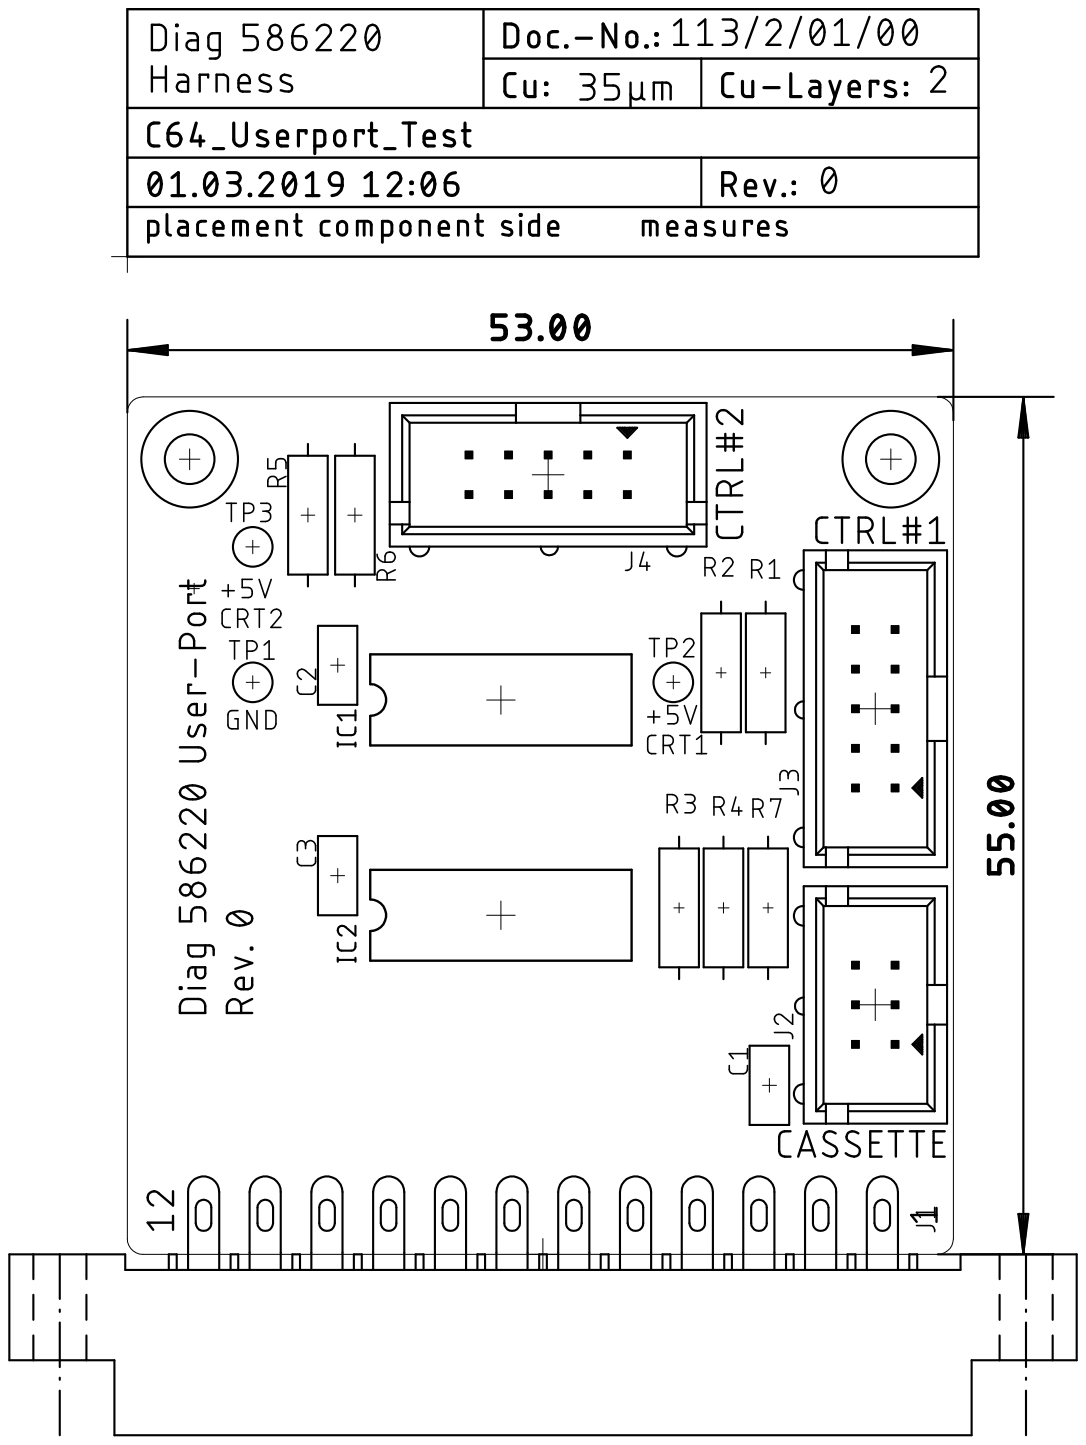
[picture p259: page 12]

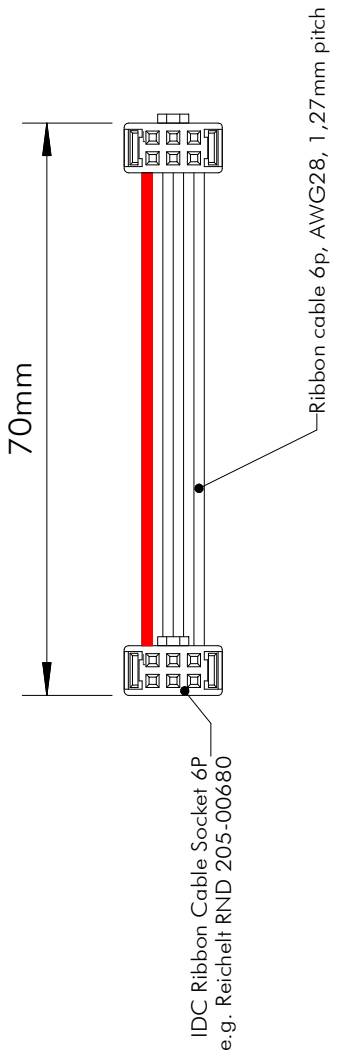
[picture p260: page 13]
File:; Titel:; Doc.-No.: 113-3-01-00; Date: 01.03.2019 16:49; Diagnostic 586220; Harness; Rev.: 0; e.g. Reichelt RND 205-00680; Port Cable

Draft.: Sven Petersen

UP-CASP.SKF

User Port - Cassette

Ribbon cable 6p, AWG28, 1,27mm pitch

IDC Ribbon Cable Socket 6P

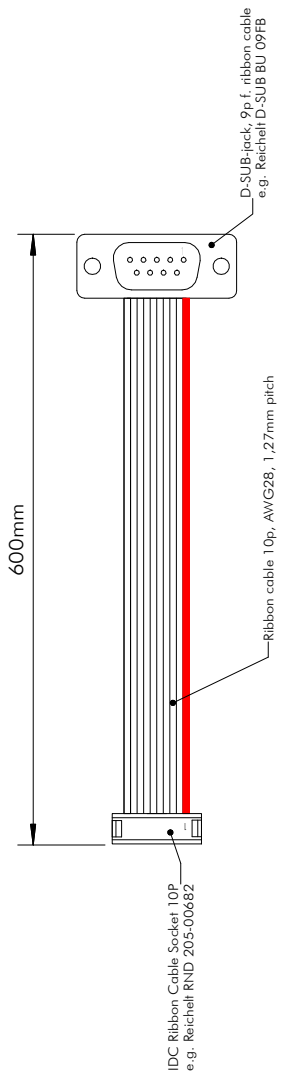
[picture p261: page 14]
File:; Titel:; Doc.-No.: 113-3-02-00; Date: 01.03.2019 16:46; Diagnostic 586220; Harness; Rev.: 0; e.g. Reichelt RND 205-00682

1 UP-CTRLP.SKF

Draft.: Sven Petersen

D-SUB-jack, 9p f. ribbon cable

e.g. Reichelt D-SUB BU 09FB

User Port - Control

Port Cable 1 1 Ribbon cable 10p, AWG28, 1,27mm pitch

IDC Ribbon Cable Socket 10P

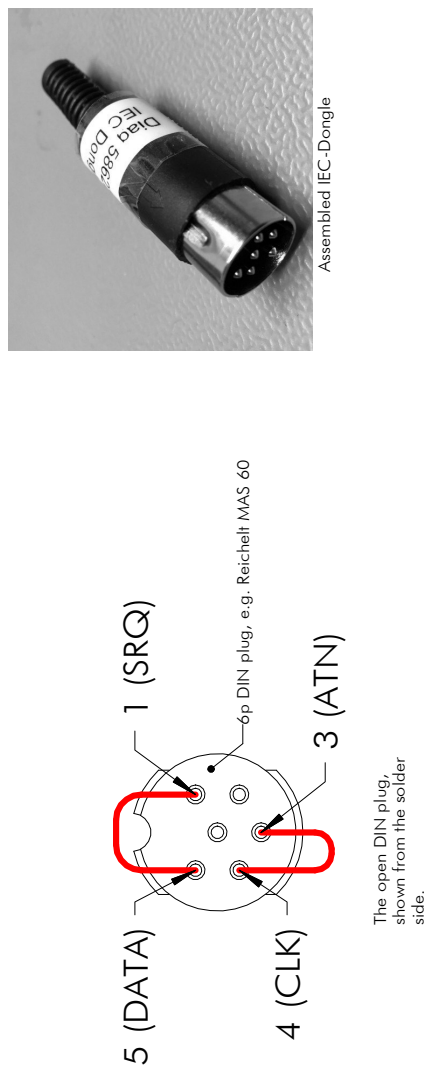
[picture p262: page 15]
File:; Titel:; Doc.-No.: 113-3-03-00; Date: 01.03.2019 18:15; Diagnostic 586220; Harness; Rev.: 0; 1 IEC.SKF; IEC-Dongle; 1 (SRQ) 5 (DATA); 3 (ATN); 4 (CLK); side.

Draft.: Sven Petersen

Assembled IEC-Dongle

6p DIN plug, e.g. Reichelt MAS 60

shown from the solder

The open DIN plug,

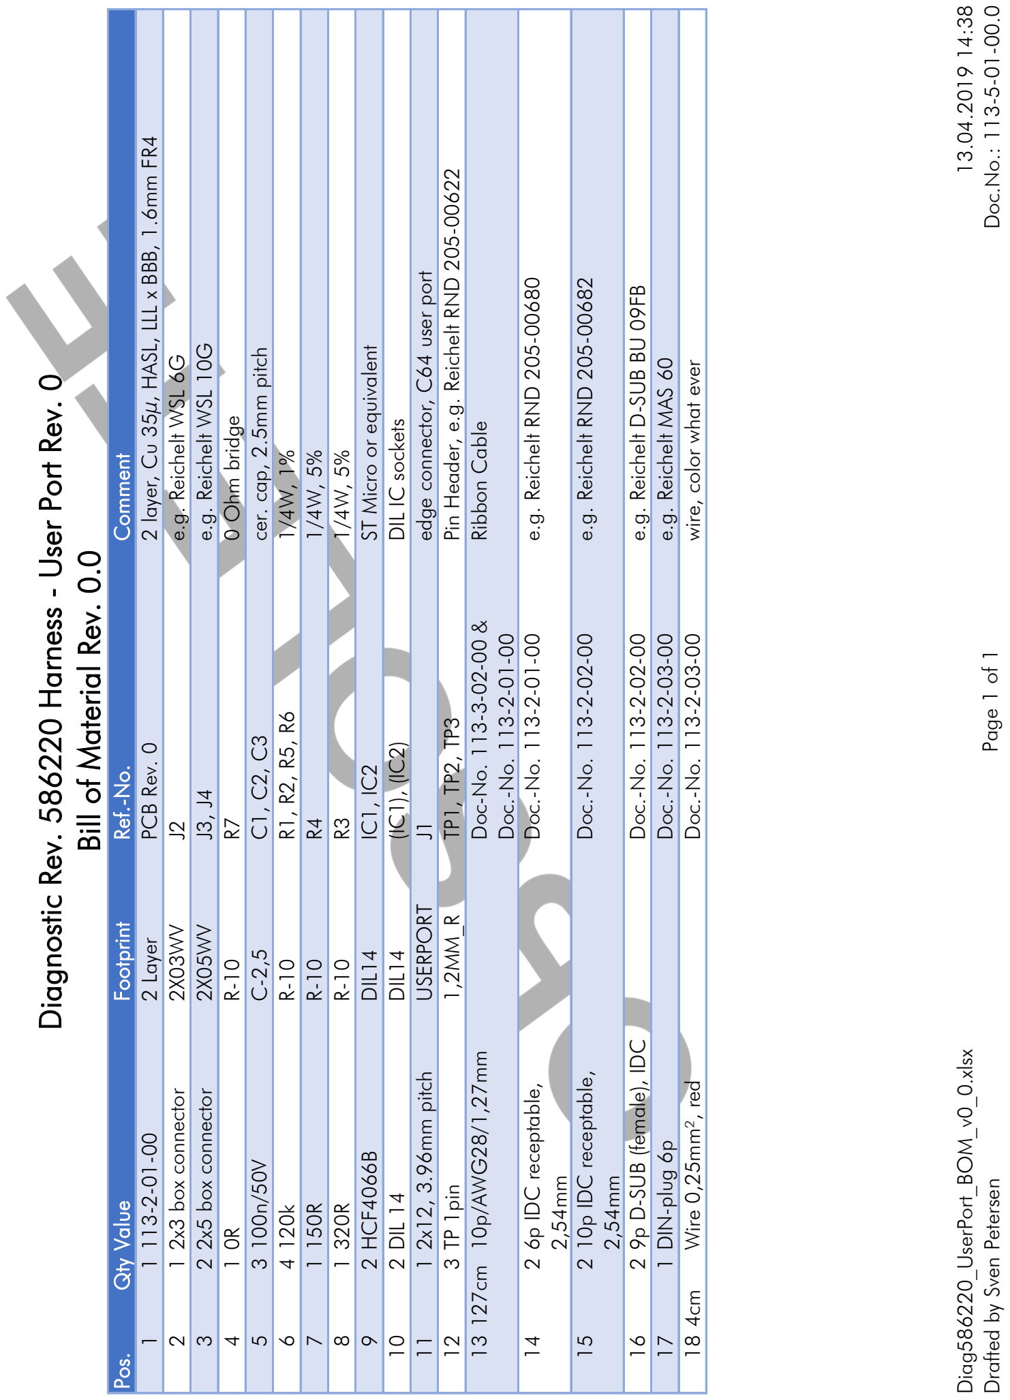
[picture p263: page 16]

Pos. Qty Value Footprint Ref.-No. Comment

1 1 113-2-01-00 2 Layer PCB Rev. 0 2 layer, Cu 35µ, HASL, LLL x BBB, 1.6mm FR4

2 1 2x3 box connector 2X03WV J2 e.g. Reichelt WSL 6G

3 2 2x5 box connector 2X05WV J3, J4 e.g. Reichelt WSL 10G

4 1 0R R-10 R7 0 Ohm bridge

5 3 100n/50V C-2,5 C1, C2, C3 cer. cap, 2.5mm pitch

6 4 120k R-10 R1, R2, R5, R6 1/4W, 1%

7 1 150R R-10 R4 1/4W, 5%

8 1 320R R-10 R3 1/4W, 5%

9 2 HCF4066B DIL14 IC1, IC2 ST Micro or equivalent

10 2 DIL 14 DIL14 (IC1), (IC2) DIL IC sockets

11 1 2x12, 3.96mm pitch USERPORT J1 edge connector, C64 user port

12 3 TP 1pin 1,2MM_R TP1, TP2, TP3 Pin Header, e.g. Reichelt RND 205-00622

13 127cm 10p/AWG28/1,27mm Doc-No. 113-3-02-00 &
Doc.-No. 113-2-01-00

Ribbon Cable

14 2 6p IDC receptable,

2,54mm

Doc.-No. 113-2-01-00 e.g. Reichelt RND 205-00680

15 2 10p IDC receptable,

2,54mm

Doc.-No. 113-2-02-00 e.g. Reichelt RND 205-00682
16 2 9p D-SUB (female), IDC Doc.-No. 113-2-02-00 e.g. Reichelt D-SUB BU 09FB

17 1 DIN-plug 6p Doc.-No. 113-2-03-00 e.g. Reichelt MAS 60
18 4cm Wire 0,25mm², red Doc.-No. 113-2-03-00 wire, color what ever

## Diagnostic Rev. 586220 Harness - User Port Rev. 0

## Bill of Material Rev. 0.0

Diag586220_UserPort_BOM_v0_0.xlsx

Drafted by Sven Petersen Page 1 of 1

13.04.2019 14:38
Doc.No.: 113-5-01-00.0

Pos. Qty Value Footprint Ref.-No. Comment

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

2 1 2x3 box connector 2X03WV J2 e.g. Reichelt WSL 6G

3 2 2x5 box connector 2X05WV J3, J4 e.g. Reichelt WSL 10G

4 1 0R R-10 R7 0 Ohm bridge

5 3 100n/50V C-2,5 C1, C2, C3 cer. cap, 2.5mm pitch

6 4 120k R-10 R1, R2, R5, R6 1/4W, 1%

7 1 150R R-10 R4 1/4W, 5%

### 8 1 320R R-10 R3 1/4W, 5% (316W works, 330W should work as well)

9 2 HCF4066B DIL14 IC1, IC2 ST Micro or equivalent

10 2 DIL 14 DIL14 (IC1), (IC2) DIL IC sockets

11 1 2x12, 3.96mm pitch USERPORT J1 edge connector, C64 user port

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

Ribbon Cable

14 2 6p IDC receptable,

2,54mm

Doc.-No. 113-2-01-00 e.g. Reichelt RND 205-00680

15 2 10p IDC receptable,

2,54mm

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

## Diagnostic Rev. 586220 Harness - User Port Rev. 0

## Bill of Material Rev. 0.1

Diag586220_UserPort_BOM_v0_1.xlsx

Drafted by Sven Petersen Page 1 of 1

13.04.2019 14:37
Doc.No.: 113-5-01-00.1

Pos. Qty Value Footprint Ref.-No. Comment

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

2 1 2x3 box connector 2X03WV J2 e.g. Reichelt WSL 6G

3 2 2x5 box connector 2X05WV J3, J4 e.g. Reichelt WSL 10G

4 1 0R R-10 R7 0 Ohm bridge

5 3 100n/50V C-2,5 C1, C2, C3 cer. cap, 2.5mm pitch

6 4 110k R-10 R1, R2, R5, R6 1/4W, 1%

7 1 150R R-10 R4 1/4W, 5%

### 8 1 316R R-10 R3 1/4W, 5% (316W works, 330W should work as well)

9 2 HCF4066B DIL14 IC1, IC2 ST Micro or equivalent

10 2 DIL 14 DIL14 (IC1), (IC2) DIL IC sockets

11 1 2x12, 3.96mm pitch USERPORT J1 edge connector, C64 user port

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

Ribbon Cable

14 2 6p IDC receptable,

2,54mm

Doc.-No. 113-2-01-00 e.g. Reichelt RND 205-00680

15 2 10p IDC receptable,

2,54mm

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

## Diagnostic Rev. 586220 Harness - User Port Rev. 0

## Bill of Material Rev. 0.2

Diag586220_UserPort_BOM_v0_2.xlsx

Drafted by Sven Petersen Page 1 of 1

14.02.2020 22:56
Doc.No.: 113-5-01-00.2
