svenpetersen1965/C64-Diagnostic-Rev.-586220-Harness/Diag586220_Harness/Diag586220_Keyboard/Rev.0/pdf/Diag_586220_Harness_Keyboard_Rev.0.pdf

Project Documentation

## Diagnostic Rev. 586220 Harness - Keyboard Dongle

Project number: 116
Revision: 0
Date: 28.02.2019

Diag586220_Keyb_ModB.docx 01.03.2019 08:29 Drafted by Sven Petersen Page 1 of 1 Doc.-No.: 116-6-01-00

### Diag 586220 Harness - Keyboard Dongle

Module Description
The Keyboard Dongle for Diag 586220 provides the required feedback connections for testing the C64’s CIA U1, which the keyboard is connected to. A LED and current limiting resistor is connected between the +5V and GND pin of the keyboard. The Restore key is connected to a dedicated line and is not tested.

Connections
20p receptacle (pitch 2.54mm)
Pin Signal Signal Pin

### 5 PB3 « PA3 17 6 PB6 « PA6 14 7 PB5 « PA5 15 8 PB4 « PA4 16 9 PB7 « PA7 20 10 PB2 « PA2 18 11 PB1 « PA1 19 12 PB0 « PA0 13

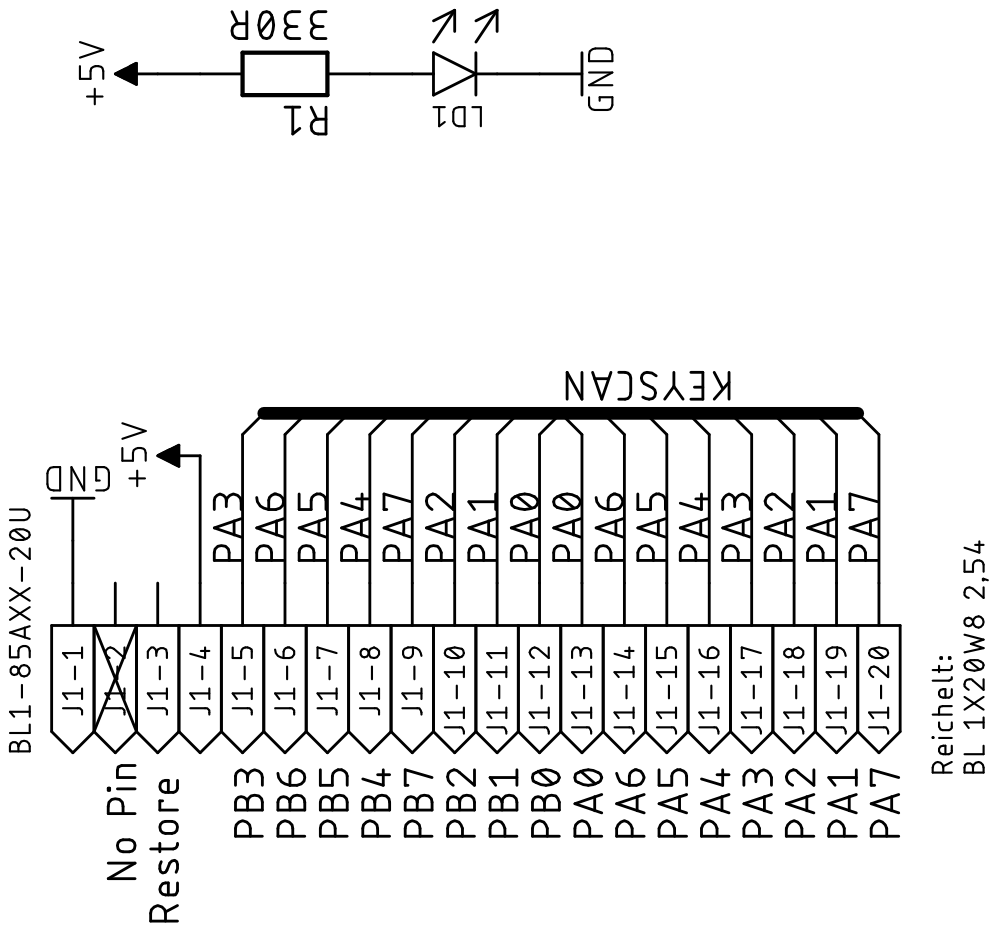
[picture p272: page 3]

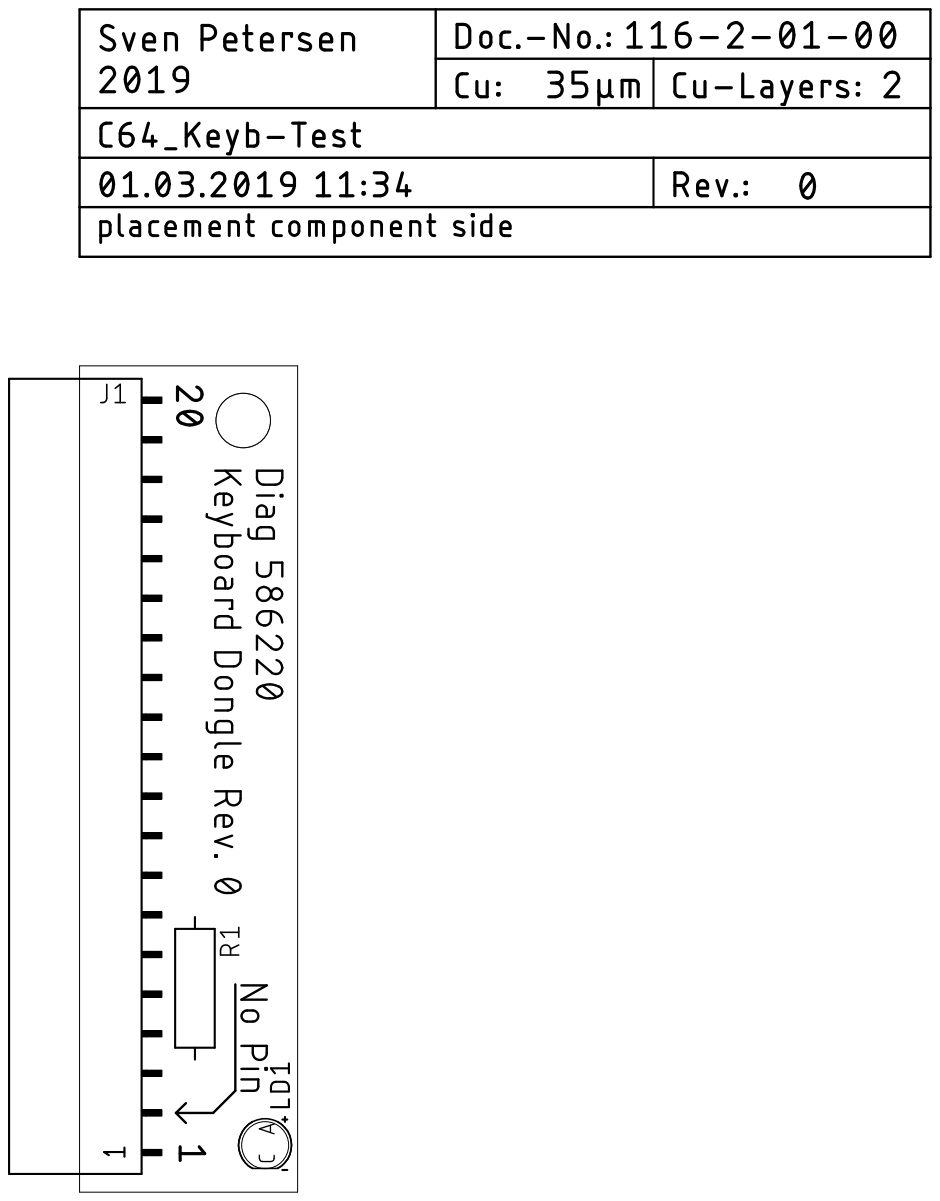
[picture p273: page 4]

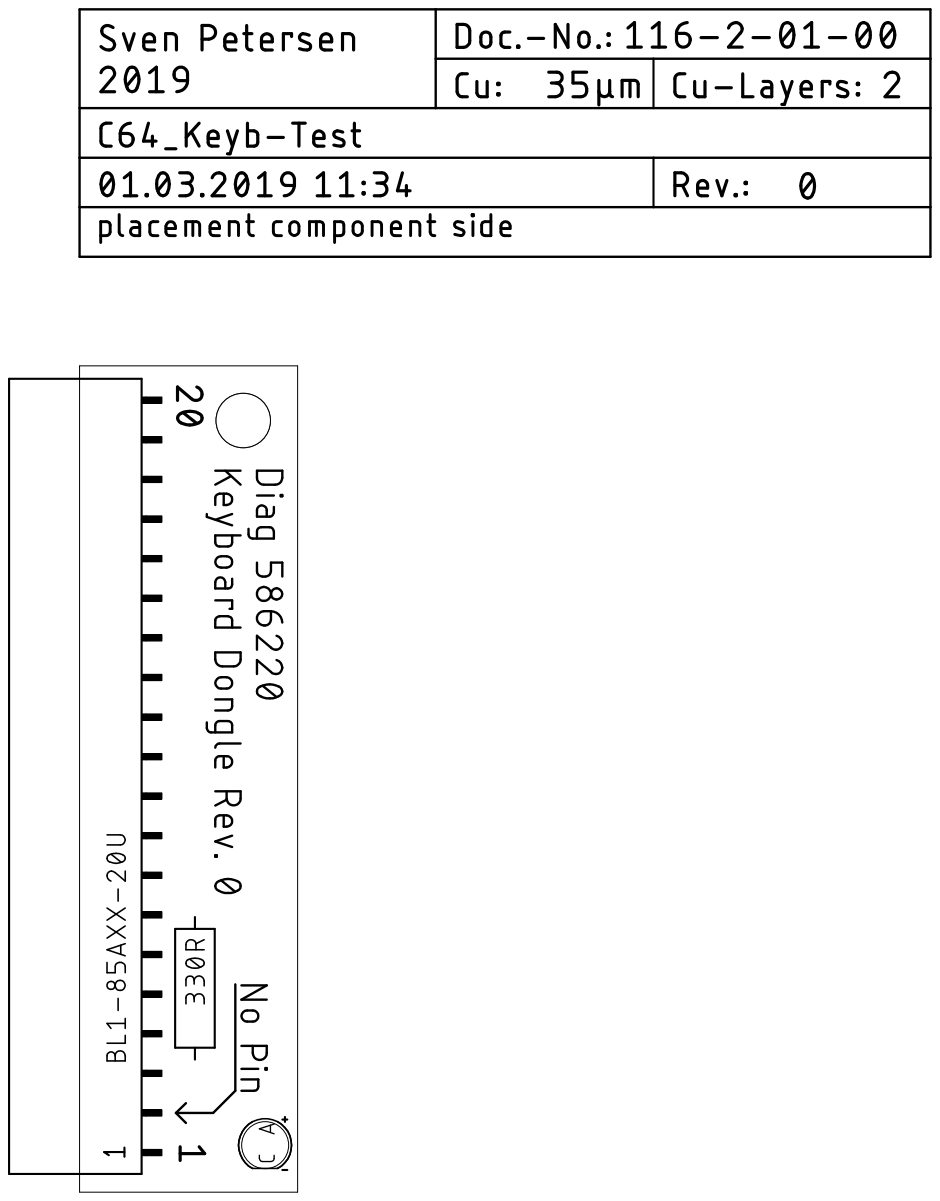
[picture p274: page 5]

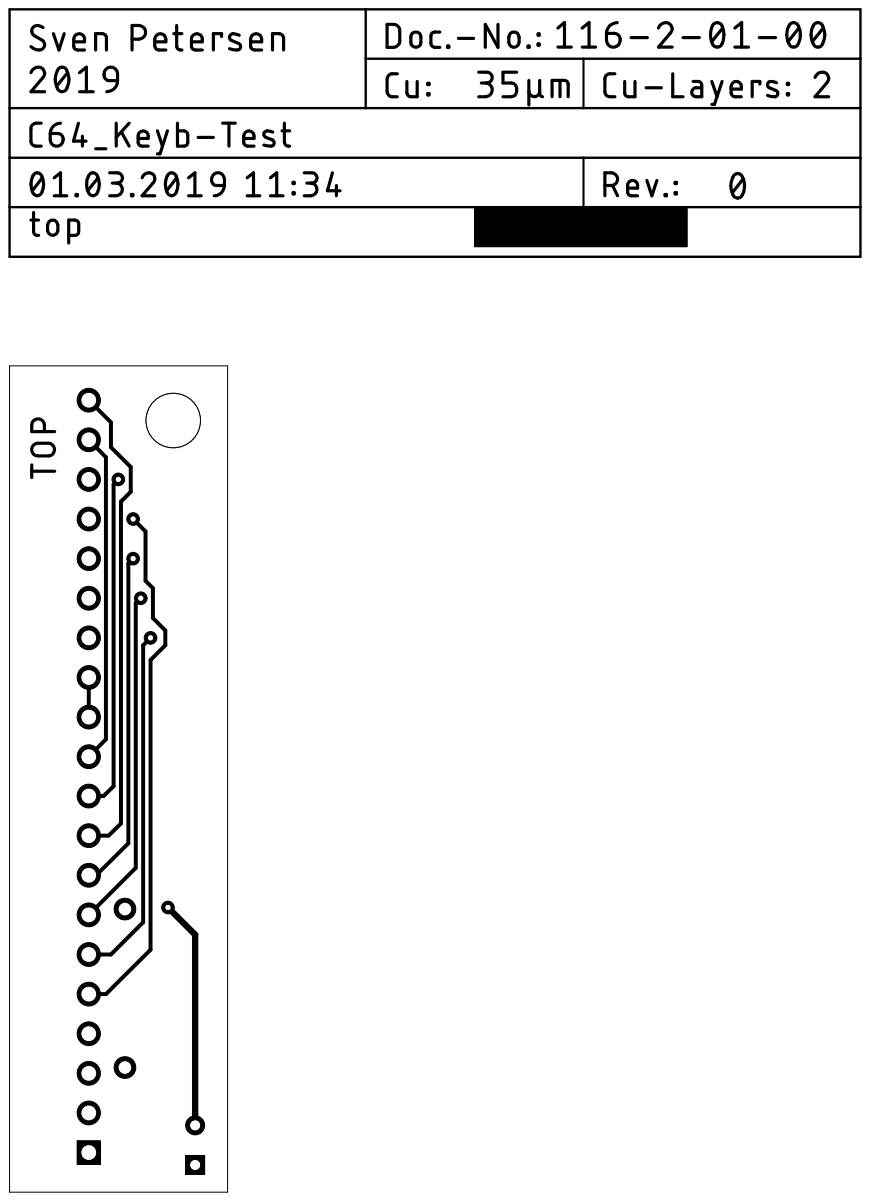
[picture p275: page 6]

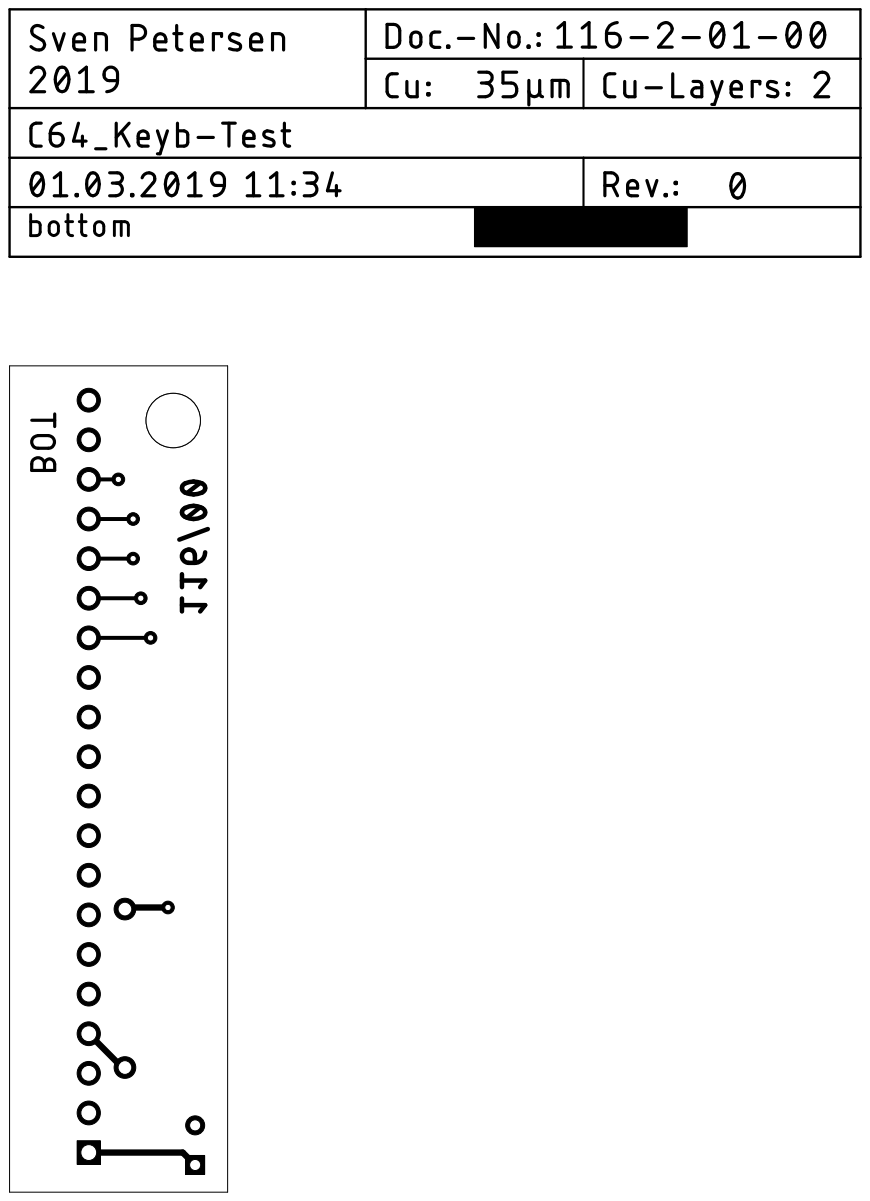
[picture p276: page 7]

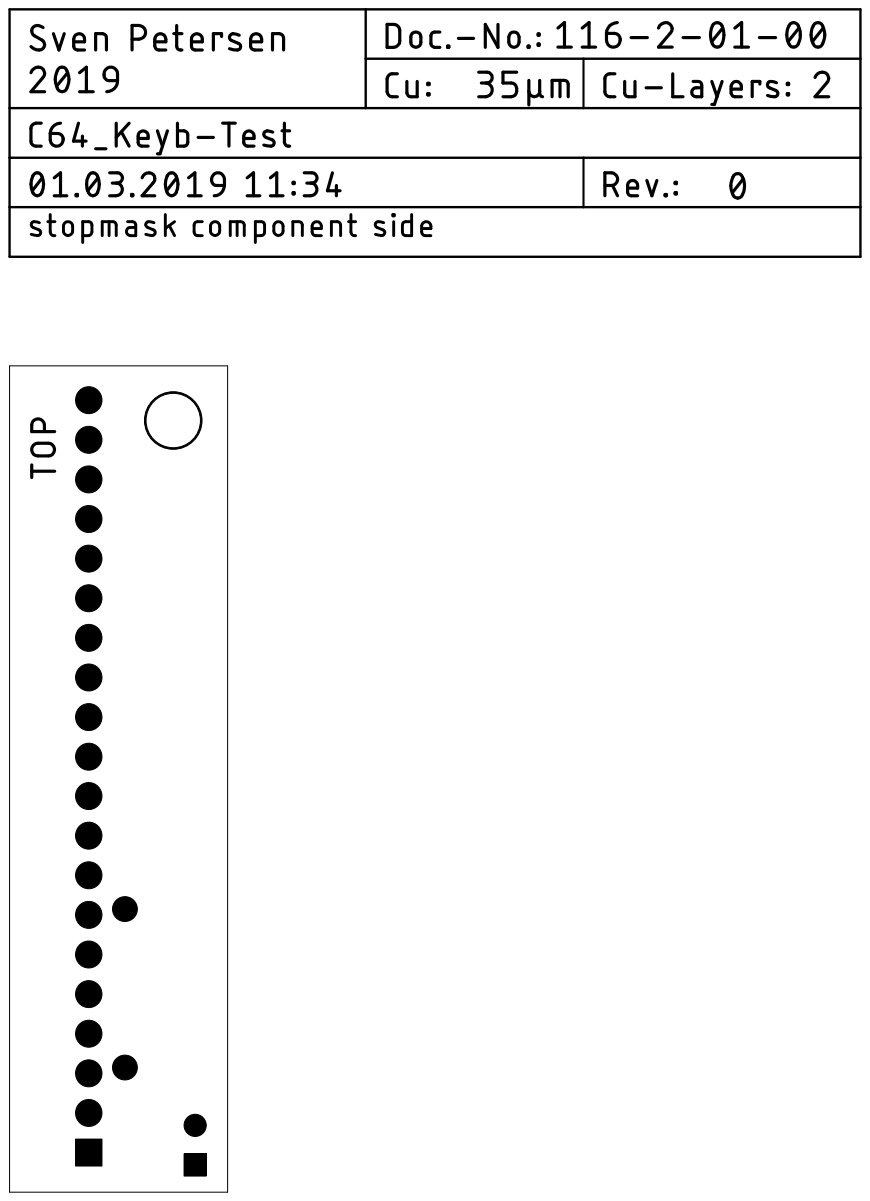
[picture p277: page 8]

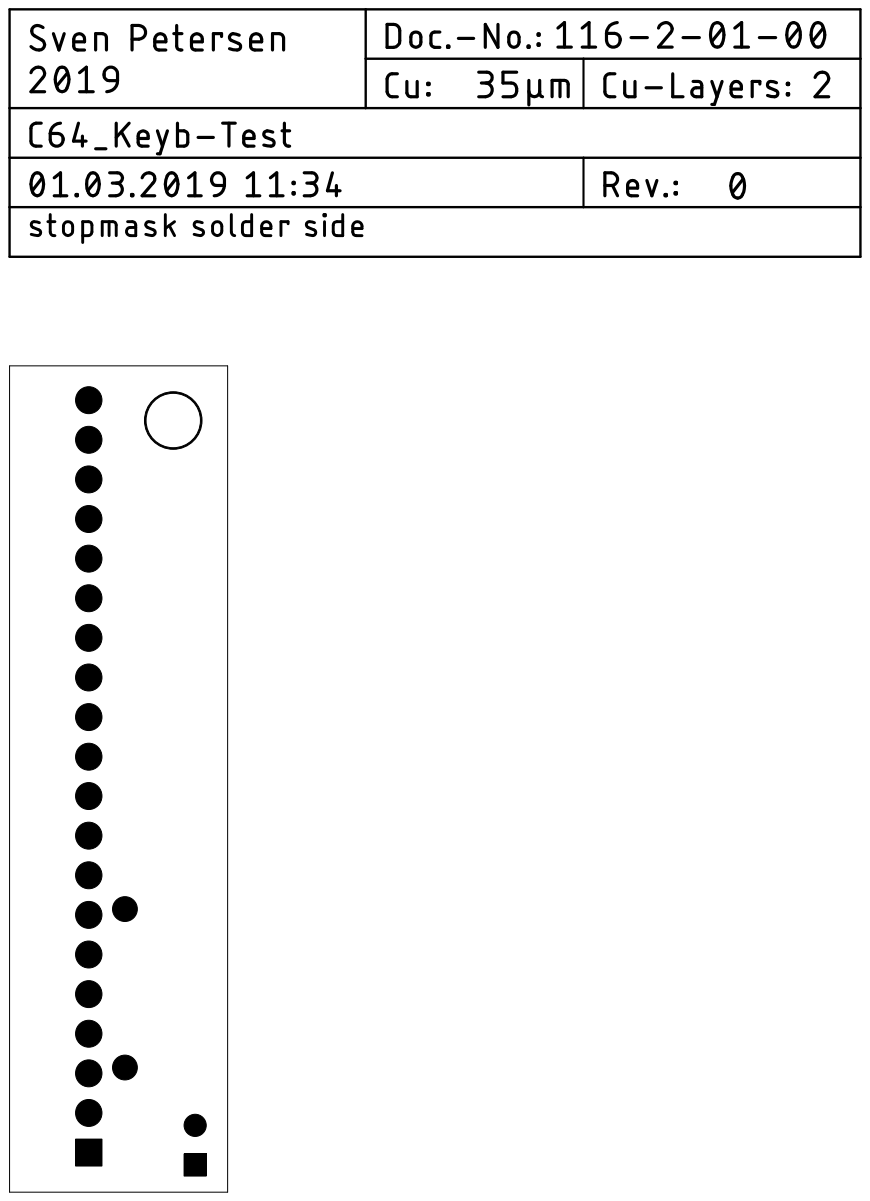
[picture p278: page 9]

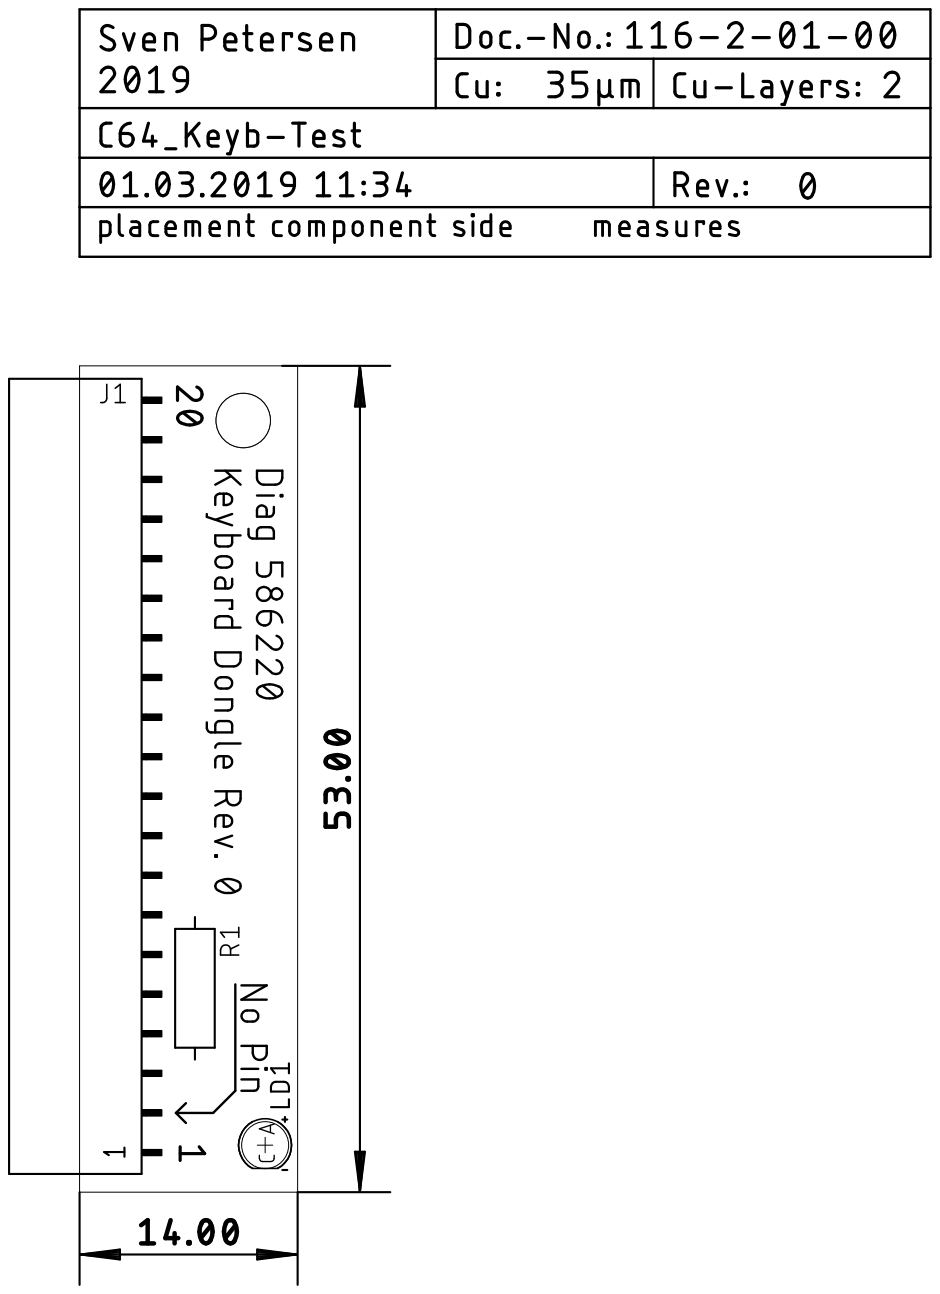
[picture p279: page 10]
