svenpetersen1965/C64-Diagnostic-Rev.-586220-Harness/Diag586220_Harness/Diag586220_Cassette_Port/Rev.0/Eagle/Diag_586220_Cassette.brd

## EAGLE design Diag586220_Harness/Diag586220_Cassette_Port/Rev.0/Eagle/Diag_586220_Cassette.brd (2019-03-14, an earlier design)

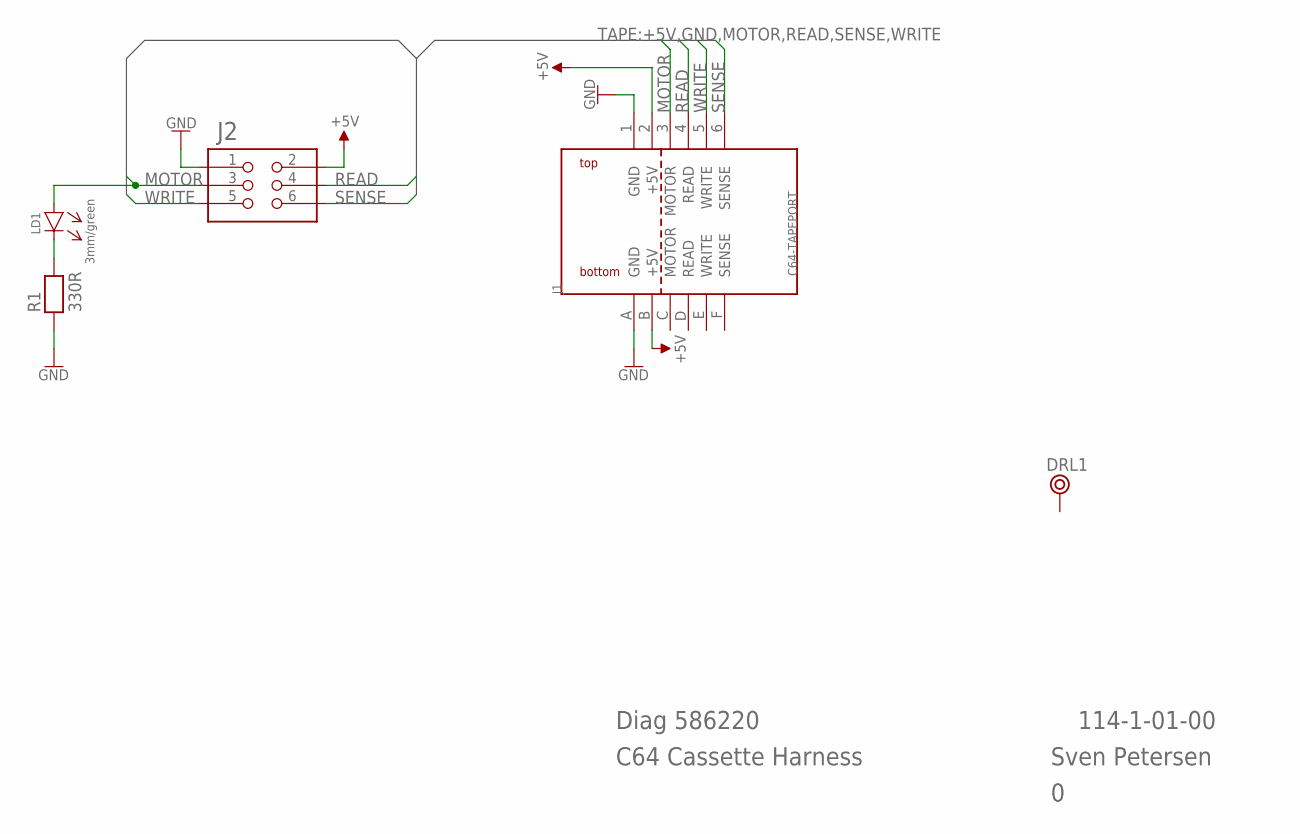
[picture p290: schematic Diag_586220_Cassette.sch]

Parts:
DRL1: BOHR3,5
J1: C64-TAPEPORT; TAPEPORT
J2: 2X03WV
LD1: 3mm/green; 3MM
R1: 330R; RS-2,5

Connections:
+5V: J1.2 (+5V), J1.B (+5V), J2.2
GND: J1.1 (GND), J1.A (GND), J2.1, R1.1
MOTOR: J1.3 (MOTOR), J2.3, LD1.A
unnamed: LD1.C (K), R1.2
READ: J1.4 (READ), J2.4
SENSE: J1.6 (SENSE), J2.6
WRITE: J1.5 (WRITE), J2.5

Notes on the sheet:
Diag 586220
C64 Cassette Harness
Sven Petersen
114-1-01-00

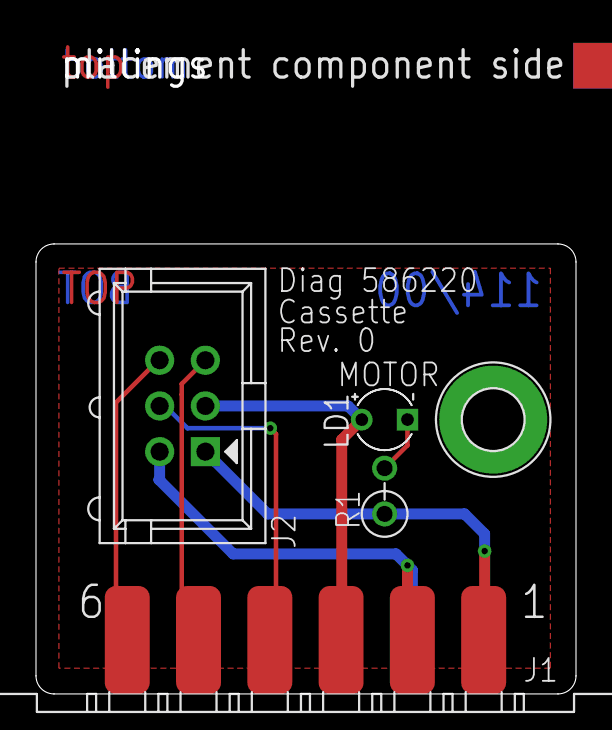
[picture p291: board Diag_586220_Cassette.brd from above]

Board: 2 copper layers, 30.0 x 25.0 mm, 7 parts (0 on the bottom side), 7 nets.

Other parts of the board:
U$5: PCB-TITLE/
U$6: 2LAYER
